mulbc/rgb-badge/hardware/coupon/rev-a/power-library-audit.md

<!-- SPDX-License-Identifier: CERN-OHL-S-2.0 -->

# Coupon Rev A power-library audit

Status: native export at `c84f8ce` completed, but visual/drawing review rejected the charger copper, converter stencil and four symbol headings. Corrections passed first-author native rendering review at `3638b1d`; independent Gate A and the documented assembler shape/stencil review remain pending. See the [correction review](../../../docs/development/power-library-review-3638b1d.md). See the [finding record](../../../docs/development/power-library-review-c84f8ce.md). The selected BQ24074/BQ24392/TS3USB31E replacement libraries now pass source/host audits and await native review; see the [replacement-library audit](power-replacement-library-audit.md) for exact maps, source hashes and recovery corrections.

## Controlled parts

Follow-on correction, 2026-09-16: the DBV0005A F.Fab body and courtyard have changed since the older native review, without copper/paste changes. New permission candidates share that package or the new DBV0006A. See the [permission-library audit](permission-library-audit.md) for the finding, corrected dimensions and pending combined native review. The BQ24074/BQ24392/TS3USB31E replacements subsequently passed [native review at c054cb4](../../../docs/development/power-replacement-review-c054cb4.md); the earlier status above describes their pre-review checkpoint.

| Function | Exact part | Package / project footprint | Controlled source |
|---|---|---|---|
| Standalone charger and NVDC power path | `BQ25616JRTWT` | TI RTW0024A WQFN24, 4 × 4 mm, 0.5 mm pitch, exposed pad / `QFN_TI_RTW0024A_4x4mm_P0.5mm_EP2.7mm` | [TI BQ25616/BQ25616J datasheet](https://www.ti.com/lit/ds/symlink/bq25616.pdf), SLUSDF7A, revised 2022-02 |
| Switched application 3.3 V buck-boost | `TPS631000DRLR` | TI DRL0008A SOT-5X3, 0.5 mm pitch / `SOT5X3_TI_DRL0008A` | [TI TPS631000 datasheet](https://www.ti.com/lit/ds/symlink/tps631000.pdf), SLVSFH3C, revised 2026-08 |
| USB-only 3.3 V LDO | `TLV75533PDBVR` | TI DBV0005A SOT-23-5 / `SOT23_TI_DBV0005A` | [TI TLV755P datasheet](https://www.ti.com/lit/ds/symlink/tlv755p.pdf), SBVS320D, revised 2024-09 |
| USB-current-state inverter | `SN74LVC1G04DBVR` | TI DBV0005A SOT-23-5 / `SOT23_TI_DBV0005A` | [TI SN74LVC1G04 datasheet](https://www.ti.com/lit/ds/symlink/sn74lvc1g04.pdf), SCES214AF, revised 2025-10 |
| Battery-current monitor | `INA232AIDDFR` | TI DDF0008A SOT-23-THIN-8 / `SOT23_THIN_TI_DDF0008A` | [TI INA232 datasheet](https://www.ti.com/lit/ds/symlink/ina232.pdf), SBOSAA2, 2022-12 |
| Four-line USB data/CC ESD | `TPD4E05U06DQAR` | TI DQA0010A USON-10 / `USON_TI_DQA0010A` | [TI TPDxE05U06 datasheet](https://www.ti.com/lit/ds/symlink/tpd4e05u06.pdf), SLVSBO7O, revised 2024-08 |
| USB-C sink/current-state detector | `TUSB320LAIRWBR` | TI RWB0012A X2QFN-12, 1.6 × 1.6 mm, 0.4 mm pitch / `X2QFN_TI_RWB0012A_1.6x1.6mm_P0.4mm` | [TI TUSB320LAI datasheet](https://www.ti.com/lit/ds/symlink/tusb320lai.pdf), SLLSEQ8D, revised 2017-05; [TI RWB package drawing](https://www.ti.com/lit/pdf/MPQF391C) |
| Switched adjustable LED-rail buck-boost | `TPS63020DSJT` | TI DSJ R-PVSON-N14, 4 × 3 mm, 0.5 mm pitch, exposed thermal pad / `VSON_TI_DSJ0014_4x3mm_P0.5mm_EP2.85x1.58mm` | [TI TPS63020 datasheet](https://www.ti.com/lit/ds/symlink/tps63020.pdf), SLVS916I, revised 2019-10 |
| Always-on single-cell fuel gauge | `MAX17048G+T10` | Maxim T822+3 TDFN-EP8, 2 × 2 mm, 0.5 mm pitch / `TDFN_Maxim_T822-3_2x2mm_P0.5mm_EP0.7x1.38mm` | [Analog Devices MAX17048/MAX17049 datasheet](https://www.analog.com/media/en/technical-documentation/data-sheets/MAX17048-MAX17049.pdf), Rev. 7, 2016-12; [21-0168 outline](https://mds.analog.com/api/public/content/tdfn-cu_21-0168.pdf); [90-0065 land pattern](https://mds.analog.com/api/public/content/tdfn-cu_90-0065.pdf) |

The manufacturer PDFs downloaded for this transcription hashed as follows. A changed upstream file requires a fresh comparison rather than a blind hash update.

| Local source name | SHA-256 |
|---|---|
| `bq25616.pdf` | `db1c80794273f68d40f13969888a1da6abc08d4a1ea38b68af8b9a09d7c9834a` |
| `tps631000.pdf` | `b52a4064a8c2cbb4c9dd97f366b398dedcb490ffc9d564245f297536a19b426b` |
| `tlv755p.pdf` | `ee739b0fe51aea50d07b53d0acccad4a0ddeac5bb7aa932bed28dc631ec5305e` |
| `sn74lvc1g04.pdf` | `ac04a53de979125799e57ea5a6dff4138fe53e0eceebe45c31f57523669887d5` |
| `ina232.pdf` | `681ab74ffec4b3b19e30363ca9be52adc75fad089d3ddad59204ebfd52574153` |
| `tpd4e05u06.pdf` | `c167cf1e72a5473a4d2c59b6a3c0251498701da05b7785919b9ceaae3b3e02c6` |
| `tusb320lai.pdf` | `62f7b3f65338e25ebd6fd46ef04474ba806b06b1cc04bc0b3d7b8191b01ca87d` |
| `MPQF391C.pdf` (RWB0012A package drawing) | `694ae75d453a97dffa48fa077e392c728dd668f625f1a7112b03b618e4017633` |
| `tps63020.pdf` | `d117773bb7370fd79377bc70ce987eec3469ea5979547a09df52fca5f95b2e69` |
| `MAX17048-MAX17049.pdf` | `70dc8eef0e012276dcdc58b6dce64af08258304bcf865ceace64e856b8029330` |
| `tdfn-cu_21-0168.pdf` | `01e449022cf1c5e20834fcf2c3587e6a8725e707eed1caa000f095e891be9b0f` |
| `tdfn-cu_90-0065.pdf` | `3448c4e9d300c7b5c2b86d6c67f19fc59c28a91c4b41dfd39fb8cc5a9d4b72eb` |

These are candidate BOM lines, not procurement or fabrication approval. Production lots must use the exact MPN through an authorized distributor or traceable PCBA supply chain. Marketplace listings may be used only for replaceable development samples and must not silently substitute a package or suffix.

## Pin transcription

The `BQ25616JRTWT` symbol preserves all 24 perimeter pins plus the exposed ground pad:

| Pins | Signals |
|---|---|
| 1–4 | `VAC`, `ACDRV`, `D+`, `D-` |
| 5–8 | open-drain `STAT`, `OTG`, open-drain `PG`, `ILIM` |
| 9–12 | active-low `CE`, `ICHG`, `TS`, `VSET` |
| 13–18 | two `BAT`, two `SYS`, two `GND` |
| 19–24 | two `SW`, `BTST`, `REGN`, `PMID`, `VBUS` |
| 25 | exposed `GND_EP` |

The symbol shows `CE` with an inversion bubble and models `STAT`/`PG` as open-collector outputs. `D+` and `D-` remain bidirectional because the charger performs analog source detection. `SW` and `BTST` are intentionally passive switching nodes. Electrical types are ERC aids, not permission to omit the datasheet-required external network.

The `TPS631000DRLR` symbol maps pins 1–8 to `VOUT`, `LX2`, `LX1`, `VIN`, `EN`, `MODE`, `GND` and `FB`. Both `EN` and `MODE` are inputs that must never float in the later circuit.

The DBV symbols do not pretend their shared five-pin package has a shared function: `TLV75533PDBVR` maps `IN`, `GND`, `EN`, `NC`, `OUT`, while `SN74LVC1G04DBVR` maps `NC`, `A`, `GND`, inverted `Y`, `VCC`. `INA232AIDDFR` preserves `IN+`, `IN-`, `GND`, `VS`, `SCL`, `SDA`, `A0`, open-drain `ALERT`. `TPD4E05U06DQAR` preserves the datasheet's `D1+`, `D1-`, `GND`, `D2+`, `D2-`, four `NC` pins and second `GND`; unused ESD pins remain explicit so a later layout cannot mistake them for protected channels.

The `TUSB320LAIRWBR` symbol maps `CC1`, `CC2`, tri-level `PORT`, `VBUS_DET`, tri-level `ADDR`, `INT_N/OUT3`, `SDA/OUT1`, `SCL/OUT2`, `ID`, `GND`, active-low `EN_N` and `VDD` in manufacturer pin order. The dual-use GPIO/I²C signals remain bidirectional in the symbol; `INT_N/OUT3` and `ID` are open-collector outputs, and `EN_N` carries an inversion bubble. These ERC types describe all supported modes and do not select the later circuit configuration.

The `TPS63020DSJT` symbol maps `VINA`, control `GND`, `FB`, two `VOUT`, two `L2`, two `L1`, two `VIN`, `EN`, `PS/SYNC`, open-drain `PG` and the exposed `PGND_EP`. VOUT pin 4 has KiCad's power-output type while pin 5 is passive, so tying the two physical output pads does not produce a false power-output-to-power-output ERC error. Both still map to their manufacturer-numbered VOUT pads. The exposed pad is assigned project pad 15 because KiCad requires a pad number even though TI names it separately from pins 1–14; every copper piece carrying 15 represents the one connected exposed thermal pad.

The `MAX17048G+T10` symbol maps `CTG`, `CELL`, `VDD`, `GND`, open-drain `ALRT`, `QSTRT`, `SCL`, `SDA` and exposed `GND_EP`. `CELL` remains passive because it is not internally connected on the one-cell MAX17048 even though the manufacturer application pin table directs it to the positive battery terminal. The exposed pad is assigned project pad 9 and must connect to ground.

## Land-pattern transcription

The RTW footprint copies TI land-pattern drawing 4211120-3/D:

- 24 signal lands are 0.28 × 0.85 mm on 0.5 mm pitch, with the row centres at ±1.975 mm;
- exposed-pad copper and mask are 2.7 × 2.7 mm and assigned to pin 25. The drawing's 3.1 mm dimension is the opening between opposing signal lands, not the exposed land; the resulting copper clearance is 0.20 mm;
- signal paste is reduced by 0.025 mm per edge to 0.23 × 0.80 mm, and signal mask margin is 0.07 mm. The project uses capsule-ended lands (0.14 mm radius); TI depicts rounded inner ends and square outer ends. This outer-end shape difference remains an explicit assembler/Gate A review item;
- thermal paste is four separate 1.1 × 1.1 mm apertures at `(±0.7, ±0.7)` mm, approximately TI's example 66% area coverage (the project lightly rounds these aperture corners);
- the package's optional nine 0.3 mm thermal vias are not embedded in the footprint. They belong in the PCB layout, where finished drill, annular ring and via fill/capping can be agreed with the assembler;
- courtyard and pin-1 marking are project review geometry, not dimensions copied into the copper pattern.

The DRL footprint copies TI drawing 4224486/G: eight 0.67 × 0.30 mm lands, left/right row centres at ±0.74 mm, and 0.5 mm vertical pitch. The project pin-1 marker sits outside the copper lands beside pad 1.

The shared DBV footprint copies TI drawing 4214839/K: five 1.10 × 0.60 mm lands, left/right row centres at ±1.30 mm, and 0.95 mm vertical pitch. The DDF footprint copies drawing 4222047/E: eight 1.05 × 0.45 mm lands with row centres at ±1.30 mm and 0.65 mm pitch.

The ESD footprint is specifically the base-suffix DQA0010A drawing 4220328/A used by `TPD4E05U06DQAR`, not the later `.B` orderable variant and its DQA0010B via-in-pad geometry. It uses ten 0.565 mm long lands at ±0.4175 mm row centres; signal/NC lands are 0.20 mm wide and ground pads 3/8 are 0.40 mm wide. Substituting a `.B`-suffixed device requires a new footprint and written review.

The RWB footprint copies TI RWB0012A drawing 4221631/B. Pins 1/2 and 7/8 use 0.70 × 0.20 mm side lands centred at `(±0.65, ±0.20)` mm; their paste-only apertures are separately encoded at 0.67 × 0.20 mm. Pins 3–6 and 9–12 use 0.20 × 0.50 mm lands on 0.40 mm pitch, centred at `y = ±0.75` mm with `x = ±0.60, ±0.20` mm. This asymmetry is intentional; the footprint is not a generic 12-pad QFN approximation.

The DSJ footprint copies package drawing 4208212-3/C, thermal-pad drawing 4208549-3/G and land-pattern drawing 4210895-2/E embedded in the current TPS63020 datasheet:

- pins 1–14 use 0.24 × 0.60 mm rounded lands on 0.50 mm pitch at `y = ±1.40` mm, with the example 0.07 mm solder-mask margin;
- exposed-pad copper is a 2.85 × 1.58 mm centre rectangle plus eight same-net 0.775 × 0.20 mm board fingers. The fingers extend the example board copper to 4.40 mm and are centred at `x = ±1.8125` mm, `y = ±0.69, ±0.23` mm;
- the thermal pad has no single full-area paste opening. The 0.125 mm stencil example is encoded as four 1.25 × 0.66 mm centre rectangles at `(±0.725, ±0.46)` mm and eight 0.85 × 0.20 mm side rectangles. These twelve primitives meet edge-to-edge to form four compound apertures, not twelve separated openings. Their total 4.66 mm² area divided by the 5.743 mm² thermal-copper area is approximately 81.14%, consistent with TI's 81% example;
- the drawing's optional 15-via example is not embedded. Via size, finished drill, fill and capping belong to PCB layout and assembler review.

The T822+3 footprint copies Analog Devices/legacy Maxim land pattern 90-0065: eight 0.80 × 0.30 mm signal lands on 0.50 mm pitch, left/right row centres 1.98 mm apart, and a 0.70 × 1.38 mm exposed land. The package-code table in the MAX17048 datasheet maps the exact TDFN orderable part to `T822+3`, outline 21-0168 and this land pattern. Drawing 90-0065 controls copper but does not specify a reduced stencil aperture; the footprint's full-area exposed-pad paste is a documented provisional default that must be reviewed with the assembler before release.

## Intentionally unresolved libraries

No unverified footprint is allowed merely to make the power sheet look complete:

- `USB4505-03-0-A`: the owner supplied GCT drawing A2; both pages and the enlarged recommended layout were visually inspected. The separate [connector audit](usb-connector-audit.md) controls the recovered symbol and draft footprint. Host mapping/geometry/fault checks and [native rendering at `bf1627c`](../../../docs/development/usb-connector-review-bf1627c.md) pass; the 0.80 mm stack-up/process qualification and undimensioned cutout reliefs remain open. The footprint contains no `Edge.Cuts`.
- The latching slide switch, remaining converter/charger passives, battery connector and NTC network remain for the next library/capture increments. The switch and battery connector cannot be frozen before exact mechanical parts are selected.

## Automated and native review

`python3 tools/check-power-libraries.py` checks twelve exact MPN properties, 132 logical pins and eleven transcribed land maps including the three replacement libraries, the BQ and DSJ exposed copper/paste splits, the DQA ground-land distinction, the RWB side-pad paste reduction and pin-1 markers. Dimension tables can repeat a transcription error: this happened at `c84f8ce`. A separate geometry guard now rejects touching/overlapping bounding boxes of distinct copper-pad numbers, independently of those tables. It is deliberately restricted to the current unrotated rectangular/rounded-rectangle power footprints and allows connected same-number thermal pieces; it is not PCB DRC. Additional checks constrain top-facing symbol headers, BQ paste/mask settings and DSJ nominal paste coverage. `tools/check-kicad.sh` also requires KiCad 10 to load and export every controlled symbol and all three footprint views.

For the native render review, verify:

- BQ pins 1–6 run down the left package edge, 7–12 across the bottom, 13–18 up the right and 19–24 across the top when viewed from above;
- BQ pin 25 is one continuous central copper/mask land, while the paste-only view shows exactly four separated square apertures;
- the BQ symbol shows the `CE` inversion bubble plus open-drain `STAT` and `PG` outputs;
- TPS631000 pad 1 is upper-left, pins 1–4 run down the left, and pins 5–8 run up the right;
- DBV/DDF pads count counter-clockwise from upper-left; both DBV parts reuse identical copper without sharing their pin names;
- DQA pads 1–5 run down the left and 6–10 run up the right, with wider ground lands only at pins 3 and 8;
- RWB pins count counter-clockwise from side pad 1; side lands are visibly longer than their paste apertures, while top/bottom lands include paste directly;
- DSJ pins 1–7 run left-to-right across the top and 8–14 right-to-left across the bottom; copper shows a centre pad with four fingers per side, while paste shows four compound thermal apertures made from twelve rectangular primitives;
- T822+3 pads 1–4 run down the left and 5–8 run up the right around the narrow exposed pad; full-area exposed-pad paste is visible and remains a documented DFM item;
- distinct copper pads remain separated, silkscreen avoids lands, and symbol headings clear their pins. Fabrication outlines and fabrication-only text may overlay copper in combined review views; they are not printed silkscreen and must not be mistaken for copper shorts.

A clean automated run is necessary but is not DRC, thermal analysis, USB compliance, assembler DFM, battery safety review or independent Gate A approval.
