mulbc/rgb-badge/hardware/coupon/rev-a/3v3-converter-capture-contract.md

<!-- SPDX-License-Identifier: CERN-OHL-S-2.0 -->

# Coupon Rev A 3.3 V application converter capture contract

Status: **provisional root-linked circuit, 2026-10-05**. The TPS631000 converter and one physical-switch control pole are now in the canonical KiCad schematic, with the former `+3V3_APP` source flag removed. The converter VIN source is still a flagged draft boundary, its EN switch/footprint remains subject to mechanical review, and no board has been built. This increment does not select the battery, charger ISET, or a PCB order. It applies the hard-OFF decision in [ADR 0004](../../../docs/decisions/0004-standalone-charging-and-hard-off-state.md), the independently switched gauge in [ADR 0015](../../../docs/decisions/0015-switch-fuel-gauge-with-application.md), the provisional parallel-capacitor target in [ADR 0017](../../../docs/decisions/0017-parallel-3v3-converter-capacitors.md), and PWR-003/004/008 in [requirements](../../../docs/requirements.md).

## Circuit boundary and defaults

| TPS631000DRLR pin | Planned net or connection | Capture condition |
|---|---|---|
| 1 VOUT | `+3V3_APP` | Output capacitor and divider upper resistor return here; do not connect to USB-only 3.3 V. |
| 2 LX2, 3 LX1 | Opposite ends of the 1 µH inductor | Short, wide switching loop per TI layout guidance; no global power labels on LX. |
| 4 VIN | Protected BQ24074 charger `OUT` / `SYS` after its voltage/permission design is completed | Input capacitor to local ground. Never connect to the gauge's `+BAT_GAUGE_SW` pole. The BQ24074 specifies 4.3–4.5 V regulated OUT with a sufficient USB input; battery-only OUT is supplied through the BAT FET. Bound switching/fault transients separately within the converter's 1.6–5.5 V operating range. |
| 5 EN | The application pole of the latching ON/OFF switch drives it high from a valid protected source; an independent resistor pulls it to GND in OFF and throughout an open/bouncing contact. | Switch contact may drive *only control current*, not application load. Candidate 100 kΩ pull-down needs an exact resistor MPN, contact and OFF-leakage audit; it is not yet captured. Do not rely on MCU GPIO or an internal pull-down. |
| 6 MODE | GND | Fixed auto-PFM default for light-load efficiency; do not float or make boot behavior firmware-dependent. |
| 7 GND | Local power return | Tie input/output capacitors and feedback lower resistor into a suitable ground layout. |
| 8 FB | Junction of 511 kΩ VOUT-to-FB and 91 kΩ FB-to-GND | Keep the sense node clear of LX and high-current traces. |

The gauge uses a **separate** switch pole for its cell feed. VLED needs the physical ON condition **and** a hardware-qualified display request, with VLED disabled at boot/reset/programming. Sharing an ON-permission signal with the LED interlock is a later reviewed circuit decision, not a reason to route LED current through the switch. When OFF, the 3.3 V converter must disconnect its output and the unpowered application must not be back-fed from USB data, gauge I²C, debug pads, or another rail. TI calls the TPS631000 behavior *true shutdown with load disconnect*, but whole-board OFF isolation and <50 µA remain measured requirements. The separately powered USB-only logic is allowed to operate when USB is attached while the application switch is OFF.

**Planned steady source states for `SYS` / converter VIN:** These are BQ24074 device behaviors from [TI's datasheet](https://www.ti.com/lit/ds/symlink/bq24074.pdf), §§8.5 and 9.3.2–9.3.4, applied to the accepted Type-C-only permission policy. They do not bound attach/detach overshoot or establish pack capability.

| State | BQ24074 OUT source | Converter-input check |
|---|---|---|
| USB absent, battery connected | Battery through BAT-to-OUT FET | Check low protected-pack end voltage, BAT-to-OUT drop and converter load capability; charging-voltage maximum is specified as 4.23 V at BAT under the datasheet condition. |
| USB-A or Type-C default-current, charger standby `(EN1, EN2) = (HI, HI)` | Battery through BAT-to-OUT FET; input FET OFF | Even with USB VBUS present, do not treat OUT as a 5 V rail or allow charger-supplied application current. Depleted/absent-pack recovery remains unguaranteed. |
| Qualified Type-C 1.5 A/3 A, charger in fixed-ILIM normal mode | Input-fed regulated OUT, **4.3–4.5 V** with sufficient headroom; DPPM may lower it, then battery supplements | Use 4.5 V for the steady high CIN DC-bias screen; check 2.7 V minimum required for TI's full-load example at discharge/DPPM corners. |
| USB input fault, source revocation or switching | Input FET turns off under standby/OVP and OUT reverts to battery when present | Capture and measure any OUT overshoot/ringing and temporary undershoot separately; 4.5 V regulated maximum is not a transient maximum. |

## Manufacturer starting point and arithmetic

TI's [TPS631000 Rev. C datasheet](https://www.ti.com/lit/ds/symlink/tps631000.pdf), §§4, 5.3, 5.5, 6.3 and 7.2, gives the 2.7–4.3 V, 3.3 V/1.5 A typical design and these proposed parts/values. The precise passive order codes below are **candidates from TI's example**, not yet audited land patterns or a released BOM.

| Function | Starting value / candidate | Unresolved qualification |
|---|---|---|
| U | `TPS631000DRLR`, already audited project-local DRL0008A library | Native circuit ERC/XML, thermal and startup validation. |
| L between LX1/LX2 | 1 µH `DFE252012P-1R0M=P2` (Murata), ±20% initial tolerance, 42 mΩ max DCR, 2.5 × 2.0 × 1.2 mm max | Murata distinguishes 4.3 A at a 30% inductance drop from **3.2 A at a 40 °C winding temperature rise**, both referenced to 20 °C ambient. The [source and land audit](3v3-inductor-footprint-audit.md) stages an unplaced exact-MPN symbol and footprint. In-enclosure thermal/current derating, native rendering and placement height remain open. |
| CIN1, CIN2 | Two parallel 22 µF `GRM187R61A226ME15` (Murata), provisional coupon target per ADR 0017 | Murata's [product/characteristic listing](https://ds.murata.com/simsurfing/mlcc.html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) lists **10 V**, X5R, ±20%, 0603, 0.8 mm height, and in-production status. TI's Table 7-4 incorrectly labels the exact-part row 6.3 V; use the manufacturer value after checking the current orderable suffix. One Murata curve shows 6.462 µF at BQ24074's 4.5 V regulated OUT maximum under the stated 25 °C condition. Exact land/placement, combined derating, charger OUT startup and transients remain unqualified. |
| COUT1, COUT2 | Two parallel 47 µF `GRM219R60J476ME44` (Murata), provisional coupon target per ADR 0017 | Murata's [part/model list](https://www.murata.com/-/media/webrenewal/tool/library/common-pdf/dynamic-model/component-list-d-mlcc-2506.ashx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) lists **6.3 V**, X5R, ±20%, 0805 and 0.95 mm maximum height. One Murata curve shows 16.876 µF at 3.3 V / 25 °C; exact land/placement, combined derating and startup/transients remain unqualified. |
| Feedback | Upper: Panasonic `ERJ2RKF5113X` (511 kΩ); lower: `ERJ2RKF9102X` (91 kΩ), proposed exact parts | Panasonic's [511 kΩ](https://industrial.panasonic.com/ww/products/pt/general-purpose-chip-resistors/models/ERJ2RKF5113X) and [91 kΩ](https://industrial.panasonic.com/ww/products/pt/general-purpose-chip-resistors/models/ERJ2RKF9102X) pages specify 0402, 0.1 W, ±1% and ±100 ppm/K each. Two project-local symbols are **staged but unplaced**, using the manufacturer's unhyphenated order codes; they reuse the earlier ERJ2 passive geometry. Native KiCad 10.0.6 rendering passed first-author visual review at [8014947](../../../docs/development/3v3-passive-library-review-8014947.md) before this text-only spelling correction; recheck their displayed values at the next converter export. Panasonic's [recommended land pattern](https://industrial.panasonic.com/cdbs/www-data/pdf/RDM0000/DMM0000COL17.pdf) (24 Dec 2025) gives a 0.5–0.6 mm inner gap, 1.4–1.6 mm outer span, and 0.4–0.6 mm land width for general-purpose ERJ 1005/0402; reused `R_Panasonic_ERJ2_0402` has 0.5, 1.5, and 0.5 mm respectively. This is a drawing comparison, not assembler approval. TI requires the lower resistor ≤100 kΩ. |
| EN pull-down | Panasonic `ERJ2RKF1003X` (100 kΩ), proposed reuse | Exact-MPN symbol and footprint already occur in the row/controller design. Check contact leakage, OFF-current budget and possible effect of VLED permission circuitry when the physical switch is specified. |

With TI's 500 mV nominal feedback reference, the nominal output is `0.500 × (1 + 511/91) = 3.3077 V`. An **illustrative, independent ±1% initial tolerance** on both resistors combined with TI's 495–505 mV reference limits gives `3.2196–3.3981 V`. For an illustrative PCB resistor excursion of **60 °C from its reference temperature**, allowing the two ±100 ppm/K TCRs to oppose each other adds ±0.6% drift *per resistor*; together with initial tolerance and the same feedback limits, the calculated range is `3.1871–3.4330 V`. This is a sensitivity screen, not a guaranteed delivered voltage or an assertion of the final PCB temperature: long-term drift, loading, routing drop, ripple and transients require a full worst-case check. Divider standing current is about `3.3077 V / (511 kΩ + 91 kΩ) = 5.49 µA` while ON; this divider belongs entirely on the switched output, so it cannot drain the battery through an enabled output in hard OFF.

**Consumer voltage screen:** The [ESP32-S3-WROOM-1U module](https://documentation.espressif.com/esp32-s3-wroom-1_wroom-1u_datasheet_en.pdf) requires 3.0–3.6 V at its supply pads; the [TLC59581](https://www.ti.com/lit/ds/symlink/tlc59581.pdf) specifies 3.0–5.5 V VCC; the [TS3USB31E application USB switch](https://www.ti.com/lit/ds/symlink/ts3usb31e.pdf) specifies 2.25–4.3 V VCC; the [INA232](https://www.ti.com/lit/ds/symlink/ina232.pdf) specifies 1.7–5.5 V; and [74HC4514](https://www.nexperia.com/product/74HC4514PW) specifies 2.0–6.0 V. These are the principal active loads identified so far, not a complete pad-by-pad audit. The illustrative static extremes leave only **187 mV below** the module's 3.0 V minimum and **167 mV above** the static 3.433 V maximum before reaching its 3.6 V upper limit. TI's 150 mV response to a 1 A load step is a *typical* advertised result, not a guaranteed maximum or a license to spend almost all 167 mV. Actual droop/overshoot at the module, RF/BLE bursts, display transitions, startup and charger/source steps must remain within every load's limits over component and temperature corners. If that cannot be shown, revisit the feedback tolerance/value or capacitance rather than accepting a marginal rail.

The candidate 100 kΩ EN pull-down, if connected as specified and if **only** the published ±0.3 µA maximum EN input bias at 5.5 V opposes it, develops at most 30 mV in OFF; TI lists a 0.5 V minimum falling threshold. This is a component-level margin illustration, **not** a bound on switch contamination, PCB leakage, an attached debug tool, or an upstream driver. In ON it draws about 27–43 µA from a 2.7–4.3 V control source; the closed switch contact must keep EN above TI's 1.2 V rising threshold at all valid SYS voltages. The pull-down must return to GND, never to unswitched SYS.

**Exact-part DC-bias evidence (owner-supplied Murata SimSurfing CSV):** `GRM219R60J476ME44_InProduction.csv`, SHA-256 `79839e9d42e739c23f68490a2ea4248ca1c6cb45026c2a8897408973abaaa57e`, contains both `GRM219R60J476ME44` and `GRM187R61A226ME15` columns. Its header states capacitance at **25 °C, AC 0.5 Vrms**. Values below are linearly interpolated between adjacent CSV samples and rounded to three decimal places; they are characteristic-curve values, not minimum specifications or board measurements.

| Candidate and DC bias | Curve capacitance | Illustrative 80% of curve | TI minimum |
|---|---:|---:|---:|
| CIN at 4.3 V | 6.811 µF | 5.449 µF | 4.2 µF |
| CIN at 4.5 V (BQ24074 regulated OUT maximum) | 6.462 µF | 5.169 µF | 4.2 µF |
| CIN at 5.0 V | 5.723 µF | 4.579 µF | 4.2 µF |
| CIN at 5.5 V | 5.131 µF | 4.105 µF | 4.2 µF |
| COUT at 3.3 V | 16.876 µF | 13.501 µF | 10.4 µF |
| COUT at 3.433 V (illustrative high static rail) | 16.133 µF | 12.906 µF | 10.4 µF |

The 80% column applies the catalog ±20% initial capacitance tolerance *as a sensitivity illustration* to the **single-part** characteristic curve; it is not a validated combined worst-case model. The [BQ24074 datasheet](https://www.ti.com/lit/ds/symlink/bq24074.pdf), §8.5, specifies **4.3–4.5 V** regulated OUT for this exact variant when the input has sufficient headroom; §9.3.4 describes lower OUT voltage under DPPM/supplement and battery-only supply. Thus 5.5 V normal USB VBUS does **not** imply 5.5 V steady converter VIN. At 4.5 V the single CIN illustration leaves 0.969 µF before temperature and aging. As a further *illustrative*, independent 15% reduction for X5R temperature variation gives 4.394 µF per CIN at 4.5 V and 10.970 µF per COUT at the illustrative 3.433 V rail high: only 0.194 and 0.570 µF respectively before aging and other effects. These multiplications are sensitivity screens, not guaranteed lower bounds. [ADR 0017](../../../docs/decisions/0017-parallel-3v3-converter-capacitors.md) provisionally doubles each position for the coupon, subject to close placement and combined manufacturer derating; two parts do not make the curve a guaranteed minimum. At the converter's 5.5 V operating input boundary a **single** CIN illustration misses the minimum by 0.095 µF even *before* the extra temperature term, but that input voltage is a fault/transient scenario, not the BQ24074's regulated steady OUT. Verify final SYS transient maximum, exact lot curves, temperature, aging and assembled rail behavior before release.

TI specifies >1.65 V for startup, but its 1.5 A example and front-page output-current claim require VIN ≥2.7 V at 3.3 V output. Do not infer full-load operation down to converter UVLO or the cell protector's cutoff. Confirm minimum `SYS` at the final protected-pack end of discharge and while source qualified charging is present, with simultaneous ESP32/radio/logic loads. TI's typical example output current is a **capability condition**, not a measured badge load or efficiency promise.

**Inductor first-order screen:** Applying TI's boost-mode Equation 3 to the *example* 1.5 A output at VIN 2.7 V, VOUT 3.3 V, assumed 90% efficiency, 0.8 µH (the candidate's nominal 1 µH minus its initial 20% tolerance), and 1.8 MHz (TI's stated minimum switching frequency) gives `D = 0.1818`, average inductor current `2.037 A`, half ripple `0.170 A` and `Ipeak ≈ 2.207 A`. TI's suggested 20% saturation margin would require `≥2.649 A` against Murata's **4.3 A 30%-drop** figure at the specified reference condition. The separate **3.2 A / +40 °C** criterion is not a board thermal result; its winding rise, local ambient, inductance under DC bias, and actual peak current must be qualified in the small enclosure. Efficiency was assumed, not measured. A pack/charger SYS below 2.7 V or a higher load needs a fresh calculation.

At the same 2.7 V / 3.3 V / 1.5 A example, replacing only the assumed efficiency in Equation 3 gives this **sensitivity screen**, not a guaranteed efficiency curve. TI's 2.6 A **minimum DC-tested** switch peak-current limit is a separate IC constraint; operating current can depend on propagation delay and external parts. The Murata 4.3 A inductance-drop and 3.2 A temperature-rise conditions are also distinct.

| Assumed efficiency | Calculated inductor peak | Margin to TI 2.6 A DC-tested minimum | TI 20% inductor saturation target |
|---:|---:|---:|---:|
| 90% | 2.207 A | 0.393 A | 2.649 A |
| 85% | 2.327 A | 0.273 A | 2.793 A |
| 80% | 2.462 A | 0.138 A | 2.955 A |
| 75% | 2.615 A | −0.015 A | 3.138 A |

This table does not establish that the badge draws 1.5 A or that efficiency falls to 75%. It shows why a full-load claim needs measured or bounded efficiency at the **actual** minimum SYS, output load and temperature, with the inductor's DC-bias inductance and winding rise considered together. The 20% saturation target is not extra margin to the IC's current limit.

## Next capture and release checks

1. The two candidate capacitor libraries have a [first-author reference-sheet audit](3v3-capacitor-footprint-audit.md): GRM18 0603 is reused, GRM21 0805 and two exact-MPN symbols are staged but unplaced. Their native export/visual review passed at [8014947](../../../docs/development/3v3-passive-library-review-8014947.md). Reconcile current approval drawings/orderable suffixes, then verify effective-capacitance curves under temperature/aging and placement. The [inductor land audit](3v3-inductor-footprint-audit.md) stages its unplaced library; check native rendering and assembler DFM. Recheck the corrected feedback symbol values during the next native export. Check the inductor-current margin against TI's worst operating-condition equation and derating, not only its table saturation value. Compare the output tolerance screen with every 3.3 V consumer's guaranteed range.
2. Finish the protected `SYS` source and exact two-pole switch (including orientation/contact sequencing), then wire VIN and EN. The USB-only rail must remain distinct. Do not make a draft PWR_FLAG look like a real `SYS` source.
3. Capture a dedicated schematic sheet, extend exported-netlist invariants to the eight IC pins, feedback network, switched enable, MODE, caps, inductor and output loads; require zero configured ERC. Inspect native KiCad 10.0.6 PDF and footprint layers. Replace/reconcile old draft supply flags at the real source boundary.
4. Before Gate A, calculate tolerance/ripple/derating and startup/inrush over minimum pack voltage, charging and 5.5 V input envelope; review hot loops, thermal copper, EMI and assembled thickness. On the coupon, log the rail **at the ESP32-S3 pads** during switch bounce, USB attach/detach, RF bursts, simultaneous LED switching and output load steps, including 3.0 V minimum and 3.6 V maximum acceptance checks with instrument bandwidth/probe method recorded. Measure OFF rail voltage and battery current both before firmware has ever run and after normal use, with USB absent and present separately.

Sources: [TI TPS631000 Rev. C (August 2026)](https://www.ti.com/lit/ds/symlink/tps631000.pdf) for electrical limits, Equation 3 and its reference circuit; [Murata DFE252012P series sheet](https://www.murata.com/~/media/webrenewal/products/inductor/chip/tokoproducts/wirewoundmetalalloychiptype/m_dfe252012p.ashx) for distinct current limits, inductance tolerance, dimensions and land-pattern sketch; Murata part/model listings linked in the table for nominal MLCC ratings; owner-supplied SimSurfing exact-part CSV identified by SHA-256 above for **25 °C DC-bias characteristics only**; [power library audit](power-library-audit.md) for the already audited IC symbol/footprint. Full temperature/aging/lot derating and assembly evidence remain to be gathered.
