mulbc/rgb-badge/CONTEXT.md

<!-- SPDX-License-Identifier: CERN-OHL-S-2.0 -->

# Project context

## Purpose

Create a small, manufacturable 48 × 16 RGB wearable badge that preserves the 1.95 mm pixel pitch of the referenced FOSSASIA Badge Magic board. The owner intends to develop the electronics, firmware and enclosure with AI assistance, then have a turnkey PCBA supplier assemble the SMT hardware.

## Complete power proposal, 2026-10-05

[ADR 0018](docs/decisions/0018-complete-power-architecture-proposal.md) and the [whole-system proposal](docs/design/power-architecture-2026-10-05.md) recommend a protected USB detector domain plus a separate reverse-blocking charger gate, the existing charger/converters, a buffered switched gauge and a lower conditional charge-current target. Status is **proposed for engineering review, not accepted as a complete power circuit**. ADR 0024 has since selected the exact protected LP452845 assembly as the Rev A design target; supplier stock and physical qualification remain open. Six consolidated holds cover pack, USB faults/inrush, permission startup, gauge transitions, hardware display interlock and thermal/fit. The limited switch/3V3 and temperature captures implement accepted directions but do not complete the charger or change an accepted current setting. Review by complete architecture → complete schematic → PCB/mechanical batches; local KiCad CLI 10.0.6 is now accessible without owner command/upload cycles. Existing reviews at `0764245` remain the baseline for preceding sheets.

**USB current coordination, 2026-10-07:** [proposed ADR 0022](docs/decisions/0022-lower-fixed-usb-input-limit-proposal.md) screens a single already-audited 3.65 kΩ BQ24074 ILIM resistor. Its calculated 0.361–0.476 A input interval avoids the earlier steady-state overlap with the published 0.850 A minimum eFuse breaker test point, before auxiliary current and resistor tolerance. This is a simpler proposed direction, not a selected schematic setting; exact-pack charge timing, input transients and default-off hardware permission remain open.

**Charger permission boundary, 2026-10-07:** The [pin-level review](docs/design/charger-permission-boundary-2026-10-07.md) maps the proposed E1 enable, AUP inhibit, supervisor RESET and BQ fixed-mode pins without connecting them to the canonical schematic. BQ `EN2` cannot yet be assigned to a qualified source with both valid-input timing and fault-voltage bounds. The current USB permission outputs remain test points, not charger controls.

**EN2 candidate, 2026-10-07:** [Proposed ADR 0023](docs/decisions/0023-charger-en2-local-clamp-proposal.md) and its [DC screen](docs/design/charger-en2-shunt-screen-2026-10-07.md) choose a local 2.5 V shunt supplied through 10 kΩ from admitted charger input as the next capture candidate. Calculated shunt-current and power margins exist within the stated input range, conditional on an assumed EN2 input-current allowance. Exact EN2 leakage at the clamped voltage, dynamic source transitions and compact-board resistor temperature remain unqualified; H3 is not closed.

**Battery-temperature sourcing update, 2026-10-05:** [ADR 0019](docs/decisions/0019-board-mounted-battery-temperature-sensing.md) accepts trialing a battery-facing PCB NTC wired directly to charger TS with a protected two-wire pack. Cell-to-board temperature error and faults must be tested before freeze; no NTC safeguard is removed. The [pack screen](docs/sourcing/pack-screen-2026-10-05.md) first identified bare-wire LiPol `LP503055` as the leading technical comparator; ADR 0024 now chooses the connectorized `LP452845` assembly for Rev A design. No pack has been ordered or qualified.

**Rev A pack/temperature direction, 2026-10-09:** [ADR 0024](docs/decisions/0024-lp452845-pack-and-temperature-window.md) selects the exact LP452845/PHR-2 drawing as the working design target. TI's BQ24074 native 10 kΩ TS window is wider than this pack's +10…+45 °C charge rating. The design now adds a battery-facing `TMP390A2DRLR` hardware hot/cold gate at nominal 40/15 °C while retaining an exact 10 kΩ Murata NTC at charger TS and its safety timer. The corrected [mechanical screen](mechanical/lp452845-swap-screen-2026-10-09.md) uses JST's actual 9.2 × 10.2 mm footprint courtyard, shifts the pack 1.5 mm right, moves one output capacitor and repacks 43 0402 boxes; this is an unrouted XY trial. Pack availability, exact polarity, continuous-discharge suitability and physical sensor-to-cell error remain unverified.

**Connected temperature subcircuit, 2026-10-10:** The [root-linked sheet](hardware/coupon/rev-a/charger-temperature.kicad_sch) connects the selected Murata NTC, TI TMP390 and AUP buffer, five supporting passives and two test pads to named `CHARGER_TS` and `CHARGER_GATE_EN` boundaries. [First-author KiCad review](docs/development/charger-temperature-capture-review-2026-10-10.md) passed zero-violation ERC, exact native XML matching 420 PCB items/1,562 logical pins, and page-15 visual inspection. BQ TS, E1 EN, the pack/header and remaining charger circuit are not connected; no temperature-protection function has been measured.

**Charger-parts follow-on, 2026-10-10:** [ADR 0024](docs/decisions/0024-lp452845-pack-and-temperature-window.md) selects exact Panasonic `ERA2AEB2491X` as the 2.49 kΩ charger ISET resistor, retaining the ±1% total resistance/current envelope; its project-local symbol uses the audited ERA2 land. The [JST `S2B-PH-SM4-TB` footprint](hardware/coupon/rev-a/jst-ph-header-library-audit.md) is staged with numbered contacts and retention lands. Exact delivered-pack polarity and mating orientation must be checked before it is connected.

**Provisional charger core, 2026-10-10:** [The root-linked BQ24074 sheet](hardware/coupon/rev-a/charger-core.kicad_sch) now joins TS to the battery-facing NTC and OUT to the application SYS net, and places exact 2.49 kΩ ISET, one 3.65 kΩ ILIM, and IN/BAT/OUT bypass parts. [ADR 0022](docs/decisions/0022-lower-fixed-usb-input-limit-proposal.md) selects the lower ILIM part for provisional capture. EN2 and EN1 are currently grounded for 100 mA fallback; ILIM is inactive until a qualified EN2 source exists. ITERM and TMR intentionally use TI's built-in termination and active safety timers. Input and protected-pack nets have explicitly draft source flags solely for ERC because neither physical gate nor pack connector is captured. KiCad 10.0.6 yielded zero configured ERC violations and complete native XML with 426 PCB items/1,589 logical pins; the 16-page export was visually reviewed. This is not a functional charger and does not resolve input gating, pack polarity, capacitor bias/voltage, thermal or Gate A.

**Final-board space finding and correction, 2026-10-05:** The [preliminary component-space screen](mechanical/component-space-screen-2026-10-05.md) moves the three LED-driver courtyards right to clear the `LP503055` body, then projects all other 151 currently captured coupon footprint instances onto the 106 × 32.5 mm trial final board. Its initial assumption that the entire battery outline must be component-free leaves 98.69 mm² nominally and 96 items unplaced in simple first-fit packing. The owner correctly noted that the pack is a separate wired assembly supported above the PCB. A conditional XY screen moving 77 0402 resistors/capacitors beneath that outline raises nominal outside-space remainder to 252.69 mm², with 22 of 74 outside items unplaced in the same crude packing pass. Height, insulation, thermal coupling and circuit locality remain unverified; neither screen proves fit or no-fit, and no requirement relaxation is justified yet.

**Grouped mechanical fit trial, 2026-10-06:** The [to-scale rear/section study](mechanical/fit-trial-2026-10-06.md) places all 32 row-switch courtyards by function and gives 77 0402 parts conditional XY positions beneath the separate LP503055 pack. Eight other captured coupon parts plus the unfinished power, connector, RF and mounting items remain unplaced; the optimistic 0402 section totals 10.75 mm of an 11 mm case with only 0.25 mm nominal margin before assembly tolerances. This is a useful layout finding, not a KiCad PCB, fit approval or reason by itself to relax the product requirements.

**Battery-connector screen, 2026-10-06:** The [JST GH/PH and Molex comparison](mechanical/battery-connector-screen-2026-10-06.md) treats each as a candidate, not a selected pack termination. An illustrative JST PH 8 × 9.6 mm pocket has no free position in the original grouped plan even before small-part first-fit. Pack availability, polarity, actual wire/crimp fit and final connector geometry remain unconfirmed.

**Connector-first follow-on, 2026-10-06:** A [Molex PicoBlade 8 × 8 mm pocket trial](mechanical/connector-first-trial-2026-10-06.md) moves the top-edge switch and decoder, then repacks the row FETs. The pocket is collision-free in XY, but only 28 of 32 row FETs fit and eleven captured parts remain unplaced overall; charger/VLED/protection/support hardware remains absent. The connector family has manufacturer AWG 28 reference-current data, but the pocket is not an audited footprint and the pack is not selected. This result directs effort back to the coupon power circuit and/or a material row-stage or battery change rather than more arbitrary first-fit movement.

**Dual row-package area screen, 2026-10-06:** [ADR 0020](docs/decisions/0020-dual-row-mosfet-package-proposal.md) proposes evaluating 16 complementary `DMC1229UFDB-7` N/P packages in place of the 32 separately packaged row FETs, without changing the captured circuit yet. The [conditional XY trial](mechanical/dual-row-package-screen-2026-10-06.md) places all retained non-row captured parts, candidate pair courtyards and four proposed power-IC package minima around the connector pocket. About 254 mm² of nominal courtyard area is recovered. Full power support, routing, copper, thermal and vertical fit are still unproven, and a real current/pin/land review must precede any coupon substitution.

**VLED placement follow-on, 2026-10-06:** The [tightened conditional screen](mechanical/dual-row-package-screen-2026-10-06.md) moves the decoder to the upper-right edge and groups the staged, default-disabled TPS63020 with all twelve passives in an 11 × 9.3 mm lower-right bay. Its first input and output capacitor centres are each 2.974 mm from the IC centre, still without routes or a switching-loop check. All sixteen proposed row-package courtyards fit the first-fit variant with the INA232 monitor IC box omitted; adding it leaves one pair box unplaced in that heuristic. [ADR 0021](docs/decisions/0021-external-battery-current-measurement.md) now accepts external current measurement and omits the on-board monitor/shunt from capture. This is not proof of complete fit: charger/input support and full routing remain absent.

**VLED routing follow-on, 2026-10-06:** A [separate local KiCad trial](docs/development/vled-routing-trial-2026-10-06.md) connects both inductor terminals and the first input/output capacitor positives with twelve 0.20 mm geometry-probe segments. Native DRC reports zero geometry violations and twenty open connections. No current/thermal suitability is established. The divider was reordered within its existing three boxes to bring its grounded end nearer the IC control-ground pad; all ground/feedback/interlock and other-board routing remain open.

**Candidate row-package library, 2026-10-06:** A [first-author Type B footprint](hardware/coupon/rev-a/dual-row-package-library-audit.md) now transcribes the manufacturer's `DMC1229UFDB-7` eight-land suggested pattern into a 3 × 3 mm project courtyard; the XY screen reads that actual candidate courtyard. Native KiCad 10.0.6 renders it and the unchanged 410-item coupon passes zero-violation ERC/1,537-pin netlist. The footprint is unpopulated; independent numeric pin-map, stencil/assembly, compact-board thermal and row-circuit review remain required before any schematic or BOM substitution.

**Provisional application-power capture, 2026-10-05:** [JS202011JCQN](hardware/coupon/rev-a/slide-switch-library-audit.md) now supplies one root-linked latching-switch control contact to the TPS631000 EN input, with a 100 kΩ OFF pull-down; the TPS631000 converter sheet is root-linked and the former `+3V3_APP` PWR_FLAG removed. Its input `+SYS_APP_IN_DRAFT` still has an explicit PWR_FLAG because charger OUT is absent. The switch's second pole and the staged gauge supply flag remain open pending I²C isolation. KiCad 10.0.6 zero-violation ERC and complete XML pass at 410 PCB items / 1,537 logical pins; pages 13–14 were visually reviewed. The vertical JCQN is not frozen for the top-edge mechanical requirement; throw direction, manufacturer land drawing, fit and OFF current remain open. This does not complete the power schematic or close the ADR 0018 holds.

## Active simplification — ADR 0013

The owner accepted **Type-C-only charging** on 2026-09-18. This section supersedes the historical BC1.2/SDP/boost descriptions below. [ADR 0013](docs/decisions/0013-type-c-only-fixed-current-charging.md) keeps OFF charging and charge-through operation only for Type-C sources advertising 1.5 A/3 A. USB-A/default-current sources provide data while ON from battery power, but no charging or charger PowerPath input. Depleted-battery USB recovery on those sources is not guaranteed.

The revised source removes BQ24392 and its support parts, eleven permission gates, three dual buffers and obsolete grant pull resistors/test pads: **47 fewer PCB items**. Current totals: **396 items / 1,492 logical pins, eleven pages**. The libraries remain 46 symbols / 27 footprints, including retained historical candidates. Native KiCad 10.0.6 at `12a134f` passed zero-violation ERC, complete exported-netlist checks and first-author visual review of the three revised USB sheets. TP21 correctly observes conditioned OUT2, closing the cb81e86 finding. See [review](docs/development/type-c-only-review-12a134f.md).

The fixed ILIM uses the audited 3.65k/3.48k precision pair permanently in parallel, with no analog switch. ADG4612 and its leakage/supply screening are historical, not active blockers. Remaining power work: protected input, VBUS qualification and physical standby control; charger/pack/NTC/timer/thermal design; converter and gauge capture; whole-port budget and layout. Flag meaningful simplification opportunities to the owner before expanding complexity.

## Active input-voltage correction — ADR 0014

[ADR 0014](docs/decisions/0014-usb-voltage-envelope-and-logic-ldo.md) corrects the normal USB upper boundary to 5.5 V. U29 now uses TPS70933DBVR with EN intentionally open; source totals remain 396 items / 1,492 logical pins, libraries 47 symbols / 27 footprints. Native U29 review passed at bad43fa; see the input-library checkpoint below. The prior 12a134f review applies to the preceding U29 circuit. [Protection screening](hardware/coupon/rev-a/usb-input-protection-screening.md) has a calculated OVLO window, but no selected/captured protection IC or transient closure. No user rerun is requested for this intermediate checkpoint. All 147 host tests passed. The owner supplied the exact-family Murata characteristic PDF; [C32 screening](hardware/coupon/rev-a/c32-characteristic-review.md) supports retaining the capacitor in the draft. The source-access blocker is closed; combined bias/temperature/aging limits and bench stability remain qualification items, not another immediate document request.

## Input-protection library checkpoint (2026-09-20)

Two unplaced TPS25947 candidates now share an audited RPW0010A library: [audit and electrical findings](hardware/coupon/rev-a/input-protection-library-audit.md). Libraries contain **49 symbols / 28 footprints**, while the schematic remains 396 items / 1,492 pins. The 472 clamp/active-limit variant could remove the OV divider now that U29 has wider input tolerance, but neither variant is selected. PG startup levels and the low end of the current threshold prevent treating nominal settings as qualification. Owner KiCad 10.0.6 at bad43fa passed configured zero-violation ERC, full native XML and first-author U29/candidate geometry review; see [evidence](docs/development/input-review-bad43fa.md). A derived RPW numbered review now removes duplicate corner numerals without changing geometry; the original native export remains unchanged. Final board assembly documentation is still a release task. No owner rerun is needed for this acceptance.

## Next functional simplification to evaluate

[Charger input gating](hardware/coupon/rev-a/charger-input-gating-assessment.md) could make the input-protection switch enforce Type-C permission, keeping the detector/logic upstream and the charger in fixed-current mode. This avoids a separate charger-mode actuator and PG receiver, but supply-domain changes, enable leakage/startup, voltage qualification and whole-port budgeting must be resolved together before an ADR/capture. The assessment provides a conditional enable-node budget and identifies why the current 10k RESET pull-up cannot be reused unchanged. A two-resistor U23 reuse screen for a whole-rail protector shows narrow illustrative DC margins; charger EN input current outside its 1.4 V test point and rail startup/transients remain unbounded. No circuit or user-facing requirement changed; no owner rerun is requested.

## Pack-current finding, 2026-09-25

[Candidate pack screen](docs/sourcing/pack-screen-2026-09-25.md) identifies a protected, NTC-equipped 700 mAh GlobTek pouch stocked by a US distributor and an 800 mAh version with its own fuel gauge. Both physically fit the rectangular envelope on paper. Their documented maximum charge currents of 700 mA and 400 mA are lower than the draft 872 mA ISET ceiling; neither can be substituted into the current charger design. The 700 mAh pack is at best a coupon candidate: the full-badge 2.49 W white-pattern model implies 0.83 A at 3.0 V, above its 0.70 A continuous discharge rating. Its drawing also needs exact-part and NTC curve confirmation. No pack is selected and no order is authorized.

The [charger thermal sensitivity screen](hardware/coupon/rev-a/charger-thermal-screen.md) shows 1.831 W idealized BQ24074 dissipation at the existing 0.872 A draft corner, 5.5 V charger IN and 3.4 V pack. The TI 44.5 °C/W reference-board figure predicts about 121.5 °C junction at an illustrative 40 °C local ambient, just below its 125 °C thermal-control point; actual compact PCB/enclosure resistance remains unknown. This is a calculated design risk, not a measured thermal result or a current-setting change.

## Current state

- 3.3 V converter capacitor checkpoint, 2026-09-30: Owner-supplied Murata SimSurfing CSV includes exact 22 µF input and 47 µF output parts. BQ24074 `OUT` regulates to at most 4.5 V in its specified steady state, while battery/standby modes feed OUT from the cell. Single-capacitor DC-bias plus illustrative tolerance/temperature calculations leave little aging margin. [ADR 0017](docs/decisions/0017-parallel-3v3-converter-capacitors.md) sets a **provisional coupon target** of two of each exact part in parallel. Manufacturer combined derating, charger OUT startup/transients and physical placement still gate selection. PWR-008 records the effective-capacitance and module-pad acceptance conditions. The historical unlinked nine-item converter candidate remains in `hardware/coupon/rev-a/staging/`; its native XML at c929711 confirmed 24 pin connections. A distinct, root-linked version with the physical-switch control pole passed [native review on 2026-10-05](docs/development/app-power-capture-review-2026-10-05.md). No physical board has been built.
- First-author passive-library review, 2026-09-30: owner-generated KiCad 10.0.6 bundle at `8014947` exported both Murata capacitor symbols, the new GRM21 footprint and previously staged Panasonic feedback symbols. [Review record](docs/development/3v3-passive-library-review-8014947.md) accepts the visible geometry and reports zero configured ERC and complete native XML for the **unchanged** staged circuit (400 PCB items / 1,507 logical pins). Exact packaging/order-code reconciliation, manufacturer combined derating, converter sheet, layout and Gate A remain open; no extra owner rerun is needed for this library checkpoint.

- Pack-selection checkpoint, 2026-09-27: [ADR 0016](docs/decisions/0016-runtime-and-fit-over-charge-speed.md) prioritizes fit and roughly six-hour runtime over the old fast-charge numbers. The [historical shortlist](docs/sourcing/pack-shortlist-2026-09-27.md) kept the documented 700 mAh GlobTek part as a conditional coupon-only candidate and the 900 mAh LiPol `LP452845` as a final-fit inquiry. Its 450 mA charge limit gives an ideal lower bound of 96 min to 80%; its continuous discharge rating and finished assembly dimensions remain unverified. ADR 0019 now supersedes that shortlist's three-wire requirement. No pack or ISET part selected; no battery order.

- Fuel-gauge decision, 2026-09-26: the owner accepted [ADR 0015](docs/decisions/0015-switch-fuel-gauge-with-application.md), disconnecting the MAX17048 from the protected cell with an independent latching-switch contact in OFF. The charger stays battery-connected for source-qualified OFF charging. PWR-003 remains <50 µA, without needing gauge firmware configuration before first battery insertion. OFF charging is not tracked by the gauge: post-ON SOC/runtime starts provisional until measured recovery is qualified. A [staged gauge sheet](hardware/coupon/rev-a/switch-gauge-boundary.md) contains the MAX17048, bypass and exact 2.2 kΩ Panasonic I²C pull-ups; its switched battery net is a **flagged draft source**, not a wired switch. The [native review at d9d717a](docs/development/gauge-review-d9d717a.md) accepts corrected rendering, zero configured ERC and full XML. Whole-bus timing and bench validation remain. Exact switch/pack/charger connection is not yet captured; PWR-003 is unverified.

- Independent layout feasibility checkpoint, 2026-09-26: the [front/rear bounding-box screen](mechanical/preliminary-placement-screen-2026-09-26.md) finds eight QT LED/USB courtyard overlaps on a centred 106 × 32.5 mm final-badge trial board. A 1.775 mm illustrative LED shift clears those *courtyard rectangles* by 0.25 mm. Rear MCU/three drivers and a 700 mAh coupon-only nominal pack have nonoverlapping trial rectangles, but the rest of the hardware, battery cables, RF, isolation and routing are not placed. This is not a KiCad PCB or final pack choice; complete schematic, board DRC and Gate A still gate fabrication.

- Requirements interview: complete.
- Architecture: accepted baseline, subject to coupon measurements.
- KiCad workflow: 10.0.6 stable baseline accepted; Coupon Rev A project and blank schematic scaffold created; the first macOS GUI round-trip opened and saved without errors, and CLI ERC reported zero violations.
- Coupon LED pair: `EAST10105RGBA0` in columns 0–7 and `QBLP1515A-RGB2A` in columns 8–15.
- Coupon LED libraries: first-author exact-MPN transcription and rendering review complete. Owner KiCad 10.0.6 exports at `27c01b4` passed pin/pad comparison; separate derived numbered views resolve body-outline/label overlap. The [review record](docs/development/led-library-review-27c01b4.md) preserves evidence and limits; independent Gate A verification remains pending.
- Coupon schematic: the matrix and TLC59581 driver passed owner KiCad 10.0.6 ERC/exported-netlist and six-page visual review at `8e95eb0`. Exact row-selection libraries passed native rendering review at `0c71860`; the complete row capture then passed zero-violation ERC, 335-item / 1,290-pin native connectivity and seven-page visual review at `eb4129b`. The exact N16R8 controller, reset/mode defaults, USB/UART boundaries and test pads passed the strict staged ERC gate, 356-item / 1,360-pin native connectivity, footprint render and eight-page visual review at `d56e1aa`. The [power pre-capture record](hardware/coupon/rev-a/power-pre-capture.md) freezes charger/current-limit and converter-divider arithmetic while keeping the USB default-current/data topology and pack-dependent NTC limits explicit. The [power-library audit](hardware/coupon/rev-a/power-library-audit.md) controls exact BQ25616J, TPS631000, TPS63020, USB-only LDO/inverter, TUSB320LAI, MAX17048, INA232 and USB ESD symbols/land patterns; corrected native rendering passed at `3638b1d`. The separately audited USB4505 candidate library passed host checks and [owner-generated native rendering review at `bf1627c`](docs/development/usb-connector-review-bf1627c.md). Input protection and remaining power circuits are uncaptured; the active USB interface increment is described below. 3.3 V N-MOS behavior plus hardware VLED inhibition remain explicit review/measurement items. See the [controller review](docs/development/controller-review-d56e1aa.md) and earlier capture/review records.
- Power-library review update: the native run at `c84f8ce` passed its staged electrical checks, but drawing/render review found a charger ground-pad short, wrong converter stencil geometry and overlapping symbol headings. The corrected native exports at `3638b1d` passed first-author review. The follow-on row layout and stale-note repairs passed native electrical and visual review at `91ef697`, closing the recorded first-author findings. PR #8 remains draft. The [finding record](docs/development/power-library-review-c84f8ce.md) also tracks the existing row-page title-block collision and stale annotations, now closed by the [native layout review](docs/development/layout-review-91ef697.md). See the [correction review](docs/development/power-library-review-3638b1d.md).
- USB/input closure: [ADR 0009](docs/decisions/0009-usb-input-current-closure.md) rejects the provisional direct BQ25616J ILIM network. [ADR 0010](docs/decisions/0010-source-qualified-off-charging.md) selects `BQ24074RGTR` + `BQ24392RSER` + `TS3USB31ERSER` + the audited `TUSB320LAIRWBR` for the next capture: fail-safe standby by default; autonomous OFF charging only from a positively classified charging source or Type-C 1.5 A/3 A source; SDP charging only while ON, configured and unsuspended. BQ24392 `GOOD_BAT` stays high with VBUS to avoid its finite dead-battery timer; the application-powered TS3USB31E supplies hard-OFF data isolation. The replacement libraries pass source/host audits and [native rendering review at c054cb4](docs/development/power-replacement-review-c054cb4.md). [ADR 0011](docs/decisions/0011-usb-total-current-headroom.md) corrects the configured-SDP current budget using low external ILIM plus a hardware-only resistor boost; the 1,024-case GPIO permission contract passes static checks. The permission gates and detector/data/LDO capture now exist; auxiliary-current proof, startup inhibition, thermal proof and remaining power capture are pending. See the [replacement-library audit](hardware/coupon/rev-a/power-replacement-library-audit.md), including the corrected unpublished geometry findings. The recovered USB4505 library and owner-generated KiCad 10.0.6 exports passed first-author review; cutout reliefs and stack-up/process qualification remain open.
- Repository workflow: owner granted standing permission on 2026-09-07 to merge PRs after applicable checks pass. LED library PR #2 through controller PR #7 are merged. Power/input is the active increment.
- Hardware testing: none.
- Native permission checkpoint: the owner-generated KiCad 10.0.6 bundle at `6d9a08b` passed first-author ERC/XML/render review: ten pages, 417 items / 1,536 logical pins and only the historical USB-boundary warning pair. See the [evidence record](docs/development/permission-review-6d9a08b.md). All seven new symbols and the corrected DBV5/DBV6 views passed; the supervisor was library-only at that checkpoint.
- USB interface checkpoint (2026-09-17): the [USB interface capture](hardware/coupon/rev-a/usb-interface-capture.md) connects the CC/BC detectors to the Schmitt logic, adds the connector/data path/ESD and USB-only LDO, and removes the old logic-supply flag. Source totals are eleven pages, 437 PCB items / 1,620 logical pin entries. Two exact Panasonic resistor symbols were added; no new footprint. The old USB ERC exceptions are retired: zero violations are required. Owner native review at `d502e65` passed zero-violation ERC and the complete XML; J1/U33 heading overlaps were found and source-corrected and closed by native review at `2bb0e08`. See the [review record](docs/development/usb-interface-review-d502e65.md). Connector VBUS and the draft +5V_USB source remain deliberately separate until input protection is designed. VBUS qualification, startup/ILIM actuation and the rest of the power section remain open.
- Logic-rail supervisor increment (2026-09-17): U34 TPS3808G01DBVR plus five passives now drives LOGIC_READY on the conditioning sheet; VBUS qualification and physical charger/ILIM inhibition remain open. Circuit totals: 443 items / 1,636 logical pins and eleven pages. [Static corner calculations and capture](hardware/coupon/rev-a/usb-supervision-capture.md) are recorded; [native review at `2bb0e08`](docs/development/logic-supervisor-review-2bb0e08.md) passed zero-violation ERC, complete XML and the supervisor/heading visual checks. The same record identifies a temperature-drift counterexample to the provisional ILIM current allocation; no current setting was raised.
- Current safe action: documentation, exact-part research, calculations and coupon design.
- Current stop condition: do not order a PCB or battery until the Gate A engineering review is complete.

- Programming-resistor increment (2026-09-17): [ADR 0012](docs/decisions/0012-programming-resistor-error-budget.md) selects three exact Panasonic ERA2AEB parts (0.1%, 25 ppm/K) while retaining ±1% total resistance error and unchanged current ceilings. Source-audited libraries now contain 45 symbols / 26 footprints; [native resistor rendering at `9e71bb5`](docs/development/precision-resistor-review-9e71bb5.md) passed. Assembly/service drift and actuator leakage still require qualification. No new circuit parts were placed. The next [actuator screening](hardware/coupon/rev-a/charger-actuator-screening.md) investigates ADG4612BCPZ-REEL7; the supplied PDF has now been visually reviewed. Its [candidate library audit](hardware/coupon/rev-a/charger-actuator-library-audit.md) adds one symbol and one project-derived footprint (46 symbols / 27 footprints total), with [native rendering at 2b7a468](docs/development/actuator-library-review-2b7a468.md) accepted. No actuator is selected or captured; intermediate-supply behavior, leakage, control loading and assembly qualification remain open.

## Non-negotiable constraints

| Area | Constraint |
|---|---|
| Matrix | 48 × 16 true RGB; pixel pitch must not exceed 1.95 mm |
| Size | Complete case no larger than 110 × 35 × 11 mm |
| Weight | Aim ≤75 g; never exceed 100 g including cell, case and magnets |
| Runtime | Roughly 6 h for the published reference workload; no automatic brightness reduction |
| Charging | USB-C at 5 V; correct A-to-C/C-to-C behaviour; charge while operating |
| Radio | BLE only in explicit programming mode |
| Controls | One momentary mode button and one latching on/off slide switch |
| OFF state | Application electronics, display and fuel gauge off; autonomous charging only from a hardware-qualified charging source (ADR 0015) |
| Assembly | Turnkey PCBA; user plugs in the protected battery and assembles the case |
| Quantity | Five assembled full badges after coupon validation |
| Budget | USD 500–800 for coupon, five badges, cells, basic test tools and shipping; case filament/design and independent review excluded |

## Accepted architecture baseline

- Three TLC59581 constant-current drivers, one per 16-column RGB block.
- Discrete four-pad common-anode RGB LEDs in a 1:16 multiplexed matrix.
- Coupon Rev A compares exact `EAST10105RGBA0` and `QBLP1515A-RGB2A` finalists at 1.95 mm pitch.
- The QBLP1515 coupon half preserves the manufacturer land pattern and alternates 0°/90° placement on a checkerboard under ADR 0008.
- Sixteen level-shifted P-channel MOSFET high-side row switches.
- ESP32-S3-WROOM-1U-N16R8 with an external 2.4 GHz FPC antenna.
- `BQ24074RGTR` standalone linear charger/PowerPath selected for capture, with thermal performance and exact pack current still requiring coupon and Gate A validation.
- `TUSB320LAIRWBR` Type-C current detection and application-powered `TS3USB31ERSER` hard-OFF data isolation. TPS70933DBVR supplies the USB-only logic domain. ADR 0013 removes BC1.2 detection and application charge grants; physical charger standby control remains uncaptured.
- TPS631000-class 3.3 V rail and TPS63020-class approximately 3.9 V LED rail.
- Switched MAX17048 fuel gauge, powering up afresh on each ON transition (ADR 0015). Battery current is measured externally during validation; no on-board INA232/shunt is populated (ADR 0021).
- Protected, keyed connectorized LiPo with hardware battery-facing NTC qualification; the sensor may be pack-integrated or PCB-mounted under ADR 0019. Capacity and exact pack remain open.
- KiCad 10.0.6 stable with project-local symbols, footprints and 3D models.

## Power states (ADRs 0013 and 0015)

| Switch | USB | Application/data | Charger input | Display |
|---|---|---|---|---|
| OFF | Absent | Off | Off | Off |
| OFF | USB-A/default/unclassified | Off | Standby | Off |
| OFF | Type-C 1.5 A/3 A | Off | Fixed-limit autonomous charging | Off |
| ON | Absent | Battery playback | Off | Fixed user brightness |
| ON | USB-A/default/unclassified | Battery operation; data if host present | Standby | Fixed user brightness |
| ON | Type-C 1.5 A/3 A | Operation; data if host present | Fixed-limit charge/PowerPath | Fixed user brightness |

These are required behaviors, not measured results. Unsupported-source USB recovery with a depleted or absent battery is not guaranteed.

## Development stages

1. **Documentation:** requirements, ADRs and candidate-part evidence.
2. **Coupon design:** production-intent 16 × 16 mixed-LED test board.
3. **Gate A review:** completed schematic plus preliminary layout reviewed independently.
4. **Coupon fabrication and bring-up:** five PCBs, three assembled.
5. **Gate B:** measured optical, electrical, thermal, runtime, RF and storage results.
6. **Full badge:** final six-layer PCB and enclosure.
7. **Gate C:** second review, frozen BOM and three comparable assembly quotes.
8. **Pilot:** five fully assembled badges.

## Open engineering decisions

- Project-local LED footprints plus pad, polarity, tape-orientation and optical-bin verification.
- Exact protected/terminated cell and connector.
- Confirm supplied TLC59581 RTQ0056E versus RTQ0056G package; qualify the nominal 4.85 mA current calculation and TI table discrepancies.
- BQ24074 fixed-current capture: permanent ILIM pair, ISET, termination, timer and exact-pack NTC network; input protection and physical standby control.
- Validation of Type-C advertisement changes, data isolation, reset/detach behavior and complete-port consumption under ADRs 0013/0014.
- Validation of the candidate `74HC4514PW,118`, `DMP2066LSN-7` and `2N7002K-7` row chain under real multiplex timing and current.
- Final USB ESD/VBUS protection topology.
- Final converter component values and layout.
- Coupon and final PCB stack-ups.
- Validation of the candidate external antenna's current gain documentation, case placement and worn RF performance.
- Winning LED, diffuser, current correction and GCLK timing after coupon tests.

## Language

- **Coupon:** the first 16 × 16 production-intent validation PCB.
- **Reference workload:** representative text/icons/animations with approximately 35% lit pixels at 25% fixed brightness.
- **Fixed brightness:** user-selected during programming; it is not changed automatically during playback.
- **Programming mode:** mode entered by holding the single button for about three seconds; BLE is enabled only in this state.
- **Release:** an immutable, hashed fabrication/assembly package tied to a tagged repository revision.

- Actuator supply analysis (2026-09-18): [conditional shared-rail calculation](hardware/coupon/rev-a/charger-actuator-supply-analysis.md) finds 0.2 V static UVLO margin, but does not close transient timing or control defaults. The ADG 17-ohm guarantee is restricted to its 4.5 V test envelope; no circuit capture or current-limit change.
