mulbc/rgb-badge/docs/development/vled-routing-trial-2026-10-06.md

<!-- SPDX-License-Identifier: CERN-OHL-S-2.0 -->

# Partial VLED routing study, 2026-10-06

The [standalone KiCad board](../../hardware/coupon/rev-a/staging/vled-routing-trial.kicad_pcb) adds twelve front-copper segments to the [13-footprint placement study](../../hardware/coupon/rev-a/staging/vled-layout-trial.kicad_pcb). [Its generator](../../tools/generate-vled-routing-trial.py) connects both IC pins for each inductor terminal, both input-capacitor positives to VIN, and the two closest output-capacitor positives to VOUT. It loads the actual schematic-net-assigned footprints and checks its copper anchor pads. Regeneration is byte-stable; board SHA-256: `a0c68c12ab34584cbf3b30aefdf774b87d43b270dab01499a8abf9b454d4a1b6`.

KiCad CLI 10.0.6's [raw native DRC report](vled-routing-drc-2026-10-06.json) shows **zero reported geometry violations and twenty unconnected items**. The previous unrouted version had thirty unconnected items. All routed segments are 0.20 mm wide and serve only to test connection and clearance geometry; no current capacity, switching performance or thermal margin is established. The board has no ground copper, feedback route, vias, interlock, LED load, other power stages or mechanical stack. It is not the coupon or final-board PCB. No physical hardware, firmware revision or measurement exists.

The initial positive-side paths can be drawn in this bay without native DRC conflicts. The next correction reorders `R84`/`R85`/`R86` within the same three 2 × 1 mm boxes, with each footprint rotated 180°. Native pad-coordinate inspection places R86's GND pad at (93.75, 23.30) mm, 3.042 mm in XY from U37's control-GND pad at (92.45, 26.05) mm; the original arrangement put that R86 pad at (99.05, 23.30) mm. R84's VLED pad is now near the outer output capacitor. This is an XY observation, not routed feedback or an electrical measurement. [TI's TPS63020 layout instructions](https://www.ti.com/lit/ds/symlink/tps63020.pdf#page=24) call for the feedback divider near control ground, short separated control-ground traces, and short/wide power and ground paths. Reserve those return paths and complete the divider, VINA and remaining output-capacitor routes before treating this as a converter layout candidate. The complete board must then receive routed DRC, thermal/current review and independent Gate A review before fabrication.
