mulbc/rgb-badge/docs/development/type-c-only-review-12a134f.md

<!-- SPDX-License-Identifier: CERN-OHL-S-2.0 -->

# Type-C-only native review at 12a134f

Reviewed 2026-09-19. Owner-generated KiCad 10.0.6 exports from `12a134f4614fc77316637105b76a50b6a3baa431`; first-author review, not independent Gate A.

## Evidence

| Artifact | SHA-256 |
|---|---|
| type-c-only-review-12a134f.zip | 3d758bd937fb2bceec46be88404eec90c384662e28991cd6dce6a601e68fa991 |
| coupon-schematic.pdf | 8c04b245152f2e3b9f1013169f60a4d71aebc15af53589a98ba31d22c5209086 |
| coupon-matrix.xml | 7930f5ef8454ad30c83eceb6c18951f495e50087ab0798ab7c2c771c5f05db50 |
| coupon-erc.rpt | bddde305323f8553b66fbfd9140acccecab6d33fa4b634466758907eadcfef0c |

The supplied terminal log identifies the source commit and reports successful ERC, XML and PDF export, with no subsequent git-status entries. ERC reports zero errors and zero warnings under the existing project configuration. It lists the existing ignored check categories (single-occurrence global labels, four-way junctions, SPICE models and footprint filters); no new exceptions were introduced by this fix.

The uploaded native XML was rerun through `tools/check-coupon-controller.py --netlist`: all 396 PCB items / 1,492 logical pins passed. This is native exported evidence, not the synthetic fixture.

## Visual review

Rendered and inspected PDF pages 9–11 (conditioning, permission and interface). No new overlaps, clipped labels or ambiguous drawn connections were found in these sheets. Page 9 shows TP21 on conditioned USB_OUT2, closing the isolated-label finding at cb81e86. Page 10 shows the reduced three-gate path and explicit test-output boundaries, with no switched ILIM branch. Page 11 shows the retained connector/ESD/CC detector, USB-only LDO and application-powered data isolator; connector VBUS and the staged protected supply remain explicitly separate. The large sheets have substantial whitespace after component removal; cosmetic repagination is deferred to avoid another low-value native checkpoint.

Unchanged pages and library geometry were not re-audited against manufacturer documents in this review. Their earlier records remain applicable only to unchanged content.

## Disposition

Accept the combined Type-C-only simplification checkpoint and close the prior OUT2 ERC finding. No source circuit changes are required from this review, and no user rerun is needed for this documentation update.

The power/input PR remains draft. Next functional work is protected input, VBUS qualification and physical charger standby/startup control, followed by charger/pack/NTC/timer/thermal and converter/gauge capture. A valid staged schematic does not establish complete power behavior, bench performance or fabrication readiness. Independent Gate A remains required.
