mulbc/rgb-badge/docs/decisions/0013-type-c-only-fixed-current-charging.md

<!-- SPDX-License-Identifier: CERN-OHL-S-2.0 -->

# ADR 0013: Type-C-only charging with one fixed input limit

- Status: Accepted by owner; capture and qualification pending
- Date: 2026-09-18
- Supersedes: ADRs 0010/0011 source policy and switched ILIM topology
- Retains: battery safeguards, current ceilings, OFF charging, operation while charging and independent Gate A

## Decision

Charge only when the Type-C source advertises 1.5 A or 3 A. USB-A connections and default-current Type-C connections do not power the system through the charger or charge the battery. Native USB data remains available while ON, with the application battery-powered when charging permission is absent. A depleted or missing battery is therefore not guaranteed to support USB recovery on an unsupported source.

Use one permanent resistor-programmed input-current limit, no switched parallel branch and no firmware charging grant. Keep BQ24074, TUSB320LAI, the USB-only logic supply and application-powered TS3USB31E isolation. Remove BQ24392 BC1.2 detection, its support parts and all BC/SDP/application-grant gates. ADG4612 is no longer needed for ILIM switching; its library remains historical candidate evidence only.

The current ceilings are not increased. Initially retain the already audited 3.65 kohm and 3.48 kohm precision resistors **permanently in parallel** as a single fixed setting: ideal calculated input range 0.834–0.975 A with the retained ±1% total resistance envelope. Two passive resistors avoid a new library/MPN review; there is no analog switch or intermediate node. A later single-resistor replacement requires its own value/tolerance check. ISET and battery prerequisites remain unchanged. The total-resistance qualification remains applicable, but switch leakage no longer contributes programming error.
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
