mulbc/rgb-badge/docs/development/actuator-library-review-2b7a468.md

<!-- SPDX-License-Identifier: CERN-OHL-S-2.0 -->

# Native actuator-library review: 2b7a468

Reviewed 2026-09-18. The candidate library rendering passes first-author review. This does not select the actuator, validate its circuit or authorize assembly.

The owner supplied `actuator-library-review-2b7a468.zip` and its KiCad 10.0.6 terminal transcript. This is the library-only source checkpoint `2b7a468b25b08fe40ad3fdfe2ccae62f4dab3cf3`.
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
