mulbc/rgb-badge/tools/check-power-libraries.py

#!/usr/bin/env python3
# SPDX-License-Identifier: Apache-2.0
"""Audit the controlled Coupon Rev A power/input component libraries.

This checks a controlled transcription of manufacturer pin tables and land
patterns. It does not approve the power architecture, schematic, PCB layout,
thermal design, assembly process or battery pack.
"""

from collections import Counter
from decimal import Decimal as D
from itertools import combinations
from pathlib import Path
import argparse
import runpy
import sys


LED = runpy.run_path(str(Path(__file__).with_name("check-led-libraries.py")))
parse, children, one = LED["parse_sexpr"], LED["children"], LED["only_child"]
property_map = LED["property_map"]
PROJECT = Path(__file__).resolve().parents[1] / "hardware" / "coupon" / "rev-a"
FP_PREFIX = "rgb-badge-coupon:"

PARTS = {
    "TPS259472ARPWR": {
        "footprint": "VQFN_TI_RPW0010A_2x2mm_HotRod",
        "datasheet": "https://www.ti.com/lit/ds/symlink/tps25947.pdf",
        "pins": {1: ("EN/UVLO", "input"), 2: ("OVCSEL", "input"),
                 3: ("PG", "open_collector"), 4: ("PGTH", "input"),
                 5: ("IN", "power_in"), 6: ("OUT", "power_out"),
                 7: ("DVDT", "output"), 8: ("GND", "power_in"),
                 9: ("ILM", "output"), 10: ("ITIMER", "output")},
    },
    "TPS259474ARPWR": {
        "footprint": "VQFN_TI_RPW0010A_2x2mm_HotRod",
        "datasheet": "https://www.ti.com/lit/ds/symlink/tps25947.pdf",
        "pins": {1: ("EN/UVLO", "input"), 2: ("OVLO", "input"),
                 3: ("PG", "open_collector"), 4: ("PGTH", "input"),
                 5: ("IN", "power_in"), 6: ("OUT", "power_out"),
                 7: ("DVDT", "output"), 8: ("GND", "power_in"),
                 9: ("ILM", "output"), 10: ("ITIMER", "output")},
    },
    "TPS70933DBVR": {
        "footprint": "SOT23_TI_DBV0005A",
        "datasheet": "https://www.ti.com/lit/ds/symlink/tps709.pdf",
        "pins": {1: ("IN", "power_in"), 2: ("GND", "power_in"),
                 3: ("EN", "input"), 4: ("NC", "passive"),
                 5: ("OUT", "power_out")},
    },
    "ADG4612BCPZ-REEL7": {
        "footprint": "LFCSP_ADI_CP16_22_3x3mm_P0.5mm_EP1.75mm",
        "datasheet": "https://www.analog.com/media/en/technical-documentation/data-sheets/ADG4612_4613.pdf",
        "pins": {0: ("GND_EP", "power_in"), 1: ("S1", "bidirectional"),
                 2: ("VSS", "power_in"), 3: ("GND", "power_in"),
                 4: ("S4", "bidirectional"), 5: ("D4", "bidirectional"),
                 6: ("IN4", "input"), 7: ("IN3", "input"),
                 8: ("D3", "bidirectional"), 9: ("S3", "bidirectional"),
                 10: ("NC", "passive"), 11: ("VDD", "power_in"),
                 12: ("S2", "bidirectional"), 13: ("D2", "bidirectional"),
                 14: ("IN2", "input"), 15: ("IN1", "input"),
                 16: ("D1", "bidirectional")},
    },
    "SN74LVC2G17DBVR": {
        "footprint": "SOT23_TI_DBV0006A",
        "datasheet": "https://www.ti.com/lit/ds/symlink/sn74lvc2g17.pdf",
        "pins": {1: ("1A", "input"), 2: ("GND", "power_in"), 3: ("2A", "input"),
                 4: ("2Y", "output"), 5: ("VCC", "power_in"), 6: ("1Y", "output")},
    },
    "SN74LVC1G00DBVR": {
        "footprint": "SOT23_TI_DBV0005A",
        "datasheet": "https://www.ti.com/lit/ds/symlink/sn74lvc1g00.pdf",
        "pins": {1: ("A", "input"), 2: ("B", "input"), 3: ("GND", "power_in"),
                 4: ("Y", "output"), 5: ("VCC", "power_in")},
    },
    "SN74LVC1G06DBVR": {
        "footprint": "SOT23_TI_DBV0005A",
        "datasheet": "https://www.ti.com/lit/ds/symlink/sn74lvc1g06.pdf",
        "pins": {1: ("NC", "passive"), 2: ("A", "input"), 3: ("GND", "power_in"),
                 4: ("Y", "open_collector"), 5: ("VCC", "power_in")},
    },
    "SN74LVC1G08DBVR": {
        "footprint": "SOT23_TI_DBV0005A",
        "datasheet": "https://www.ti.com/lit/ds/symlink/sn74lvc1g08.pdf",
        "pins": {1: ("A", "input"), 2: ("B", "input"), 3: ("GND", "power_in"),
                 4: ("Y", "output"), 5: ("VCC", "power_in")},
    },
    "SN74LVC1G11DBVR": {
        "footprint": "SOT23_TI_DBV0006A",
        "datasheet": "https://www.ti.com/lit/ds/symlink/sn74lvc1g11.pdf",
        "pins": {1: ("A", "input"), 2: ("GND", "power_in"), 3: ("B", "input"),
                 4: ("Y", "output"), 5: ("VCC", "power_in"), 6: ("C", "input")},
    },
    "SN74LVC1G32DBVR": {
        "footprint": "SOT23_TI_DBV0005A",
        "datasheet": "https://www.ti.com/lit/ds/symlink/sn74lvc1g32.pdf",
        "pins": {1: ("A", "input"), 2: ("B", "input"), 3: ("GND", "power_in"),
                 4: ("Y", "output"), 5: ("VCC", "power_in")},
    },
    "TPS3808G01DBVR": {
        "footprint": "SOT23_TI_DBV0006A",
        "datasheet": "https://www.ti.com/lit/ds/symlink/tps3808.pdf",
        "pins": {1: ("RESET", "open_collector"), 2: ("GND", "power_in"),
                 3: ("MR", "input"), 4: ("CT", "input"),
                 5: ("SENSE", "input"), 6: ("VDD", "power_in")},
    },
    "BQ24074RGTR": {
        "footprint": "VQFN_TI_RGT0016C_3x3mm_P0.5mm_EP1.68mm",
        "datasheet": "https://www.ti.com/lit/ds/symlink/bq24074.pdf",
        "pins": {
            1: ("TS", "input"), 2: ("BAT", "power_in"), 3: ("BAT", "power_in"),
            4: ("CE", "input"), 5: ("EN2", "input"), 6: ("EN1", "input"),
            7: ("PGOOD", "open_collector"), 8: ("VSS", "power_in"),
            9: ("CHG", "open_collector"), 10: ("OUT", "power_out"),
            11: ("OUT", "passive"), 12: ("ILIM", "input"), 13: ("IN", "power_in"),
            14: ("TMR", "input"), 15: ("ITERM", "input"), 16: ("ISET", "bidirectional"),
            17: ("VSS_EP", "power_in"),
        },
    },
    "BQ24392RSER": {
        "footprint": "UQFN_TI_RSE0010A_2x1.5mm_P0.5mm",
        "datasheet": "https://www.ti.com/lit/ds/symlink/bq24392.pdf",
        "pins": {
            1: ("SW_OPEN", "open_collector"), 2: ("DM_HOST", "bidirectional"),
            3: ("DP_HOST", "bidirectional"), 4: ("CHG_AL_N", "open_collector"),
            5: ("GOOD_BAT", "input"), 6: ("GND", "power_in"),
            7: ("DP_CON", "bidirectional"), 8: ("DM_CON", "bidirectional"),
            9: ("VBUS", "power_in"), 10: ("CHG_DET", "output"),
        },
    },
    "TS3USB31ERSER": {
        "footprint": "UQFN_TI_RSE0008A_1.5x1.5mm_P0.5mm",
        "datasheet": "https://www.ti.com/lit/ds/symlink/ts3usb31e.pdf",
        "pins": {
            1: ("OE", "input"), 2: ("HSD+", "bidirectional"),
            3: ("D+", "bidirectional"), 4: ("GND", "power_in"),
            5: ("D-", "bidirectional"), 6: ("HSD-", "bidirectional"),
            7: ("NC", "passive"), 8: ("VCC", "power_in"),
        },
    },
    "BQ25616JRTWT": {
        "footprint": "QFN_TI_RTW0024A_4x4mm_P0.5mm_EP2.7mm",
        "datasheet": "https://www.ti.com/lit/ds/symlink/bq25616.pdf",
        "pins": {
            1: ("VAC", "power_in"), 2: ("ACDRV", "output"),
            3: ("D+", "bidirectional"), 4: ("D-", "bidirectional"),
            5: ("STAT", "open_collector"), 6: ("OTG", "input"),
            7: ("PG", "open_collector"), 8: ("ILIM", "input"),
            9: ("CE", "input"), 10: ("ICHG", "input"),
            11: ("TS", "input"), 12: ("VSET", "input"),
            13: ("BAT", "power_in"), 14: ("BAT", "power_in"),
            15: ("SYS", "power_out"), 16: ("SYS", "power_out"),
            17: ("GND", "power_in"), 18: ("GND", "power_in"),
            19: ("SW", "passive"), 20: ("SW", "passive"),
            21: ("BTST", "passive"), 22: ("REGN", "power_out"),
            23: ("PMID", "power_out"), 24: ("VBUS", "power_in"),
            25: ("GND_EP", "power_in"),
        },
    },
    "TPS631000DRLR": {
        "footprint": "SOT5X3_TI_DRL0008A",
        "datasheet": "https://www.ti.com/lit/ds/symlink/tps631000.pdf",
        "pins": {
            1: ("VOUT", "power_out"), 2: ("LX2", "passive"),
            3: ("LX1", "passive"), 4: ("VIN", "power_in"),
            5: ("EN", "input"), 6: ("MODE", "input"),
            7: ("GND", "power_in"), 8: ("FB", "input"),
        },
    },
    "TLV75533PDBVR": {
        "footprint": "SOT23_TI_DBV0005A",
        "datasheet": "https://www.ti.com/lit/ds/symlink/tlv755p.pdf",
        "pins": {
            1: ("IN", "power_in"), 2: ("GND", "power_in"),
            3: ("EN", "input"), 4: ("NC", "passive"),
            5: ("OUT", "power_out"),
        },
    },
    "SN74LVC1G04DBVR": {
        "footprint": "SOT23_TI_DBV0005A",
        "datasheet": "https://www.ti.com/lit/ds/symlink/sn74lvc1g04.pdf",
        "pins": {
            1: ("NC", "passive"), 2: ("A", "input"),
            3: ("GND", "power_in"), 4: ("Y", "output"),
            5: ("VCC", "power_in"),
        },
    },
    "INA232AIDDFR": {
        "footprint": "SOT23_THIN_TI_DDF0008A",
        "datasheet": "https://www.ti.com/lit/ds/symlink/ina232.pdf",
        "pins": {
            1: ("IN+", "input"), 2: ("IN-", "input"),
            3: ("GND", "power_in"), 4: ("VS", "power_in"),
            5: ("SCL", "input"), 6: ("SDA", "bidirectional"),
            7: ("A0", "input"), 8: ("ALERT", "open_collector"),
        },
    },
    "TPD4E05U06DQAR": {
        "footprint": "USON_TI_DQA0010A",
        "datasheet": "https://www.ti.com/lit/ds/symlink/tpd4e05u06.pdf",
        "pins": {
            1: ("D1+", "passive"), 2: ("D1-", "passive"),
            3: ("GND", "power_in"), 4: ("D2+", "passive"),
            5: ("D2-", "passive"), 6: ("NC", "passive"),
            7: ("NC", "passive"), 8: ("GND", "power_in"),
            9: ("NC", "passive"), 10: ("NC", "passive"),
        },
    },
    "TUSB320LAIRWBR": {
        "footprint": "X2QFN_TI_RWB0012A_1.6x1.6mm_P0.4mm",
        "datasheet": "https://www.ti.com/lit/ds/symlink/tusb320lai.pdf",
        "pins": {
            1: ("CC1", "bidirectional"), 2: ("CC2", "bidirectional"),
            3: ("PORT", "input"), 4: ("VBUS_DET", "input"),
            5: ("ADDR", "input"), 6: ("INT_N/OUT3", "open_collector"),
            7: ("SDA/OUT1", "bidirectional"), 8: ("SCL/OUT2", "bidirectional"),
            9: ("ID", "open_collector"), 10: ("GND", "power_in"),
            11: ("EN_N", "input"), 12: ("VDD", "power_in"),
        },
    },
    "TPS63020DSJT": {
        "footprint": "VSON_TI_DSJ0014_4x3mm_P0.5mm_EP2.85x1.58mm",
        "datasheet": "https://www.ti.com/lit/ds/symlink/tps63020.pdf",
        "pins": {
            1: ("VINA", "power_in"), 2: ("GND", "power_in"),
            3: ("FB", "input"), 4: ("VOUT", "power_out"),
            # One common VOUT pin is passive in ERC to avoid connecting
            # two power-output symbols on the same physical output rail.
            5: ("VOUT", "passive"), 6: ("L2", "passive"),
            7: ("L2", "passive"), 8: ("L1", "passive"),
            9: ("L1", "passive"), 10: ("VIN", "power_in"),
            11: ("VIN", "power_in"), 12: ("EN", "input"),
            13: ("PS/SYNC", "input"), 14: ("PG", "open_collector"),
            15: ("PGND_EP", "power_in"),
        },
    },
    "MAX17048G+T10": {
        "footprint": "TDFN_Maxim_T822-3_2x2mm_P0.5mm_EP0.7x1.38mm",
        "datasheet": "https://www.analog.com/media/en/technical-documentation/data-sheets/MAX17048-MAX17049.pdf",
        "pins": {
            1: ("CTG", "power_in"), 2: ("CELL", "passive"),
            3: ("VDD", "power_in"), 4: ("GND", "power_in"),
            5: ("ALRT", "open_collector"), 6: ("QSTRT", "input"),
            7: ("SCL", "input"), 8: ("SDA", "bidirectional"),
            9: ("GND_EP", "power_in"),
        },
    },
}


def require(condition, message):
    if not condition:
        raise ValueError(message)


def library_pins(symbol):
    result = {}
    for unit in children(symbol, "symbol"):
        for pin in children(unit, "pin"):
            number = one(pin, "number", "pin")[1]
            require(number not in result, f"duplicate library pin {number}")
            result[number] = pin
    return result


def footprint(project, name):
    path = project / "footprints" / "rgb-badge-coupon.pretty" / f"{name}.kicad_mod"
    return parse(path)


def dec(values):
    return tuple(map(D, values))


def pad_position(pad):
    return dec(one(pad, "at", "pad")[1:3])


def pad_size(pad):
    return dec(one(pad, "size", "pad")[1:])


def pad_layers(pad):
    return one(pad, "layers", "pad")[1:]


def check_copper_separation(root):
    """Conservative bounding-box check, independent of the dimension audit.

    Only current unrotated rectangular/rounded lands are supported. Same-number
    thermal fingers may intentionally meet. This is not board-level KiCad DRC.
    """
    pads = [p for p in children(root, "pad") if "F.Cu" in pad_layers(p)]
    for pad in pads:
        require(pad[1] and pad[3] in ("rect", "roundrect"),
                f"{root[1]}: unsupported copper pad geometry")
        at = one(pad, "at", "pad")
        require(len(at) == 3 or D(at[3]) == 0,
                f"{root[1]}: rotated copper pad needs a geometry-aware check")
    for a, b in combinations(pads, 2):
        if a[1] == b[1]:
            continue
        ap, bp = pad_position(a), pad_position(b)
        az, bz = pad_size(a), pad_size(b)
        gaps = [abs(ap[i] - bp[i]) - (az[i] + bz[i]) / 2 for i in (0, 1)]
        require(max(gaps) > 0,
                f"{root[1]}: copper pads {a[1]}/{b[1]} touch or overlap in bounding boxes")


def check_symbol_header_clearance(symbol):
    """Reserve a full text-height above top-facing pin endpoints."""
    pins = library_pins(symbol)
    top = [D(one(p, "at", "pin")[2]) for p in pins.values()
           if D(one(p, "at", "pin")[3]) == 270]
    if not top:
        return
    fields = {p[1]: p for p in children(symbol, "property")}
    value = fields["Value"]
    height = D(one(one(one(value, "effects", "value"), "font", "font"), "size", "font")[2])
    value_y = D(one(value, "at", "value")[2])
    reference_y = D(one(fields["Reference"], "at", "reference")[2])
    require(value_y - height / 2 >= max(top) + height,
            f"{symbol[1]}: header overlaps top-pin keepout")
    require(reference_y - value_y >= 2 * height,
            f"{symbol[1]}: reference/value header spacing too small")


def check_symbol_libraries(project):
    library = parse(project / "symbols" / "rgb-badge-coupon.kicad_sym")
    symbols = {symbol[1]: symbol for symbol in children(library, "symbol")}
    for mpn, audit in PARTS.items():
        require(mpn in symbols, f"missing exact power symbol {mpn}")
        symbol = symbols[mpn]
        properties = property_map(symbol)
        require(properties.get("MPN") == mpn, f"{mpn}: MPN property mismatch")
        require(properties.get("Footprint") == FP_PREFIX + audit["footprint"],
                f"{mpn}: footprint property mismatch")
        require(properties.get("Datasheet") == audit["datasheet"],
                f"{mpn}: datasheet property mismatch")
        pins = library_pins(symbol)
        check_symbol_header_clearance(symbol)
        require(set(pins) == set(map(str, audit["pins"])), f"{mpn}: pin numbers mismatch")
        for number, (name, electrical_type) in audit["pins"].items():
            pin = pins[str(number)]
            require(one(pin, "name", f"{mpn}.{number}")[1] == name,
                    f"{mpn}.{number}: pin name mismatch")
            require(pin[1] == electrical_type, f"{mpn}.{number}: electrical type mismatch")
    require(library_pins(symbols["BQ25616JRTWT"])["9"][2] == "inverted",
            "BQ25616J CE must show active-low inversion")
    for mpn, number in (("BQ24074RGTR", "4"), ("BQ24392RSER", "4"),
                        ("TS3USB31ERSER", "1")):
        require(library_pins(symbols[mpn])[number][2] == "inverted",
                f"{mpn}.{number} must show active-low inversion")
    require(library_pins(symbols["SN74LVC1G04DBVR"])["4"][2] == "inverted",
            "SN74LVC1G04 output must show inversion")
    require(library_pins(symbols["TUSB320LAIRWBR"])["11"][2] == "inverted",
            "TUSB320LAI EN_N must show active-low inversion")
    for mpn in ("SN74LVC1G00DBVR", "SN74LVC1G06DBVR", "SN74LVC1G08DBVR",
                "SN74LVC1G11DBVR", "SN74LVC1G32DBVR"):
        expected = "inverted" if mpn in ("SN74LVC1G00DBVR", "SN74LVC1G06DBVR") else "line"
        require(library_pins(symbols[mpn])["4"][2] == expected,
                f"{mpn}: output inversion mismatch")
    for number in ("1", "3"):
        require(library_pins(symbols["TPS3808G01DBVR"])[number][2] == "inverted",
                f"TPS3808G01DBVR.{number} must show active-low inversion")
    for number in ("4", "6"):
        require(library_pins(symbols["SN74LVC2G17DBVR"])[number][2] == "line",
                f"SN74LVC2G17DBVR.{number}: non-inverting buffer output required")
    adg = symbols["ADG4612BCPZ-REEL7"]
    require(property_map(adg).get("Manufacturer") == "Analog Devices", "ADG manufacturer mismatch")
    for number in ("6", "7", "14", "15"):
        require(library_pins(adg)[number][2] == "line", "ADG4612 controls must be active high")
    return symbols


def check_rtw_footprint(project):
    root = footprint(project, "QFN_TI_RTW0024A_4x4mm_P0.5mm_EP2.7mm")
    pads = children(root, "pad")
    numbered = {pad[1]: pad for pad in pads if pad[1]}
    require(set(numbered) == set(map(str, range(1, 26))), "RTW pad numbers mismatch")
    for number in range(1, 25):
        pad = numbered[str(number)]
        if number <= 6:
            position = (D("-1.975"), D("-1.25") + D("0.5") * (number - 1))
            size = (D("0.85"), D("0.28"))
        elif number <= 12:
            position = (D("-1.25") + D("0.5") * (number - 7), D("1.975"))
            size = (D("0.28"), D("0.85"))
        elif number <= 18:
            position = (D("1.975"), D("1.25") - D("0.5") * (number - 13))
            size = (D("0.85"), D("0.28"))
        else:
            position = (D("1.25") - D("0.5") * (number - 19), D("-1.975"))
            size = (D("0.28"), D("0.85"))
        require(pad_position(pad) == position, f"RTW pad {number} position mismatch")
        require(pad_size(pad) == size, f"RTW pad {number} size mismatch")
        require(pad_layers(pad) == ["F.Cu", "F.Paste", "F.Mask"],
                f"RTW pad {number} layer mismatch")
        require(D(one(pad, "solder_paste_margin", "RTW pad")[1]) == D("-0.025"),
                f"RTW pad {number} signal paste reduction mismatch")
        require(D(one(pad, "solder_mask_margin", "RTW pad")[1]) == D("0.07"),
                f"RTW pad {number} mask margin mismatch")
        require(D(one(pad, "roundrect_rratio", "RTW pad")[1]) == D("0.5"),
                f"RTW pad {number} corner radius mismatch")
    ep = numbered["25"]
    require(pad_position(ep) == (D("0"), D("0")), "RTW exposed-pad position mismatch")
    require(pad_size(ep) == (D("2.7"), D("2.7")), "RTW exposed-pad size mismatch")
    require(pad_layers(ep) == ["F.Cu", "F.Mask"], "RTW exposed-pad layers mismatch")
    paste = [pad for pad in pads if not pad[1]]
    require(len(paste) == 4, "RTW stencil aperture count mismatch")
    require({pad_position(pad) for pad in paste} == {
        (D("-0.7"), D("-0.7")), (D("0.7"), D("-0.7")),
        (D("-0.7"), D("0.7")), (D("0.7"), D("0.7")),
    }, "RTW stencil aperture positions mismatch")
    require(all(pad_size(pad) == (D("1.1"), D("1.1")) for pad in paste),
            "RTW stencil aperture size mismatch")
    require(all(pad_layers(pad) == ["F.Paste"] for pad in paste),
            "RTW stencil aperture layers mismatch")
    marker = one(root, "fp_circle", "RTW pin-1 marker")
    require(dec(one(marker, "center", "RTW pin-1 marker")[1:]) == (D("-2.45"), D("-1.65")),
            "RTW pin-1 marker mismatch")


def check_replacement_geometry(root, body, courtyard, marker):
    """Also guard radius and outline errors invisible to the pad-size tables."""
    require(D(one(root, "solder_mask_margin", "footprint")[1]) == D("0.05"),
            f"{root[1]} mask margin mismatch")
    for pad in children(root, "pad"):
        require(pad[3] == "roundrect", f"{root[1]} pad shape mismatch")
        radius = min(pad_size(pad)) * D(one(pad, "roundrect_rratio", "pad")[1])
        require(abs(radius - D("0.05")) <= D("0.000001"),
                f"{root[1]} pad {pad[1]} corner radius mismatch")
        for override in ("solder_mask_margin", "solder_paste_margin",
                         "solder_paste_margin_ratio"):
            require(not children(pad, override), f"{root[1]} unexpected pad {override}")
    for override in ("solder_paste_margin", "solder_paste_margin_ratio"):
        require(not children(root, override), f"{root[1]} unexpected footprint {override}")
    for layer, extent in (("F.Fab", body), ("F.CrtYd", courtyard)):
        rectangles = [r for r in children(root, "fp_rect")
                      if one(r, "layer", "rectangle")[1] == layer]
        require(len(rectangles) == 1, f"{root[1]} {layer} outline count mismatch")
        require(dec(one(rectangles[0], "start", "rectangle")[1:]) == tuple(-v for v in dec(extent))
                and dec(one(rectangles[0], "end", "rectangle")[1:]) == dec(extent),
                f"{root[1]} {layer} outline mismatch")
    circle = one(root, "fp_circle", "pin-1 marker")
    require(dec(one(circle, "center", "circle")[1:]) == dec(marker)
            and one(circle, "layer", "circle")[1] == "F.SilkS",
            f"{root[1]} pin-1 marker mismatch")


def check_rgt_footprint(project):
    root = footprint(project, PARTS["BQ24074RGTR"]["footprint"])
    pads = children(root, "pad")
    require(Counter(p[1] for p in pads) == Counter([*map(str, range(1, 18)), ""]),
            "RGT0016C pad numbers mismatch")
    numbered = {p[1]: p for p in pads}
    for number in range(1, 17):
        j = (number - 1) % 4
        if number <= 4:
            position, size = (D("-1.4"), D("-0.75") + D("0.5") * j), dec(("0.6", "0.24"))
        elif number <= 8:
            position, size = (D("-0.75") + D("0.5") * j, D("1.4")), dec(("0.24", "0.6"))
        elif number <= 12:
            position, size = (D("1.4"), D("0.75") - D("0.5") * j), dec(("0.6", "0.24"))
        else:
            position, size = (D("0.75") - D("0.5") * j, D("-1.4")), dec(("0.24", "0.6"))
        pad = numbered[str(number)]
        require(pad_position(pad) == position, f"RGT0016C pad {number} position mismatch")
        require(pad_size(pad) == size, f"RGT0016C pad {number} size mismatch")
        require(pad_layers(pad) == ["F.Cu", "F.Paste", "F.Mask"],
                f"RGT0016C pad {number} layers mismatch")
    for number, size, layers in (("17", "1.68", ["F.Cu", "F.Mask"]),
                                  ("", "1.55", ["F.Paste"])):
        pad = numbered[number]
        require(pad_position(pad) == dec(("0", "0")), "RGT0016C central pad position mismatch")
        require(pad_size(pad) == (D(size), D(size)), "RGT0016C central pad size mismatch")
        require(pad_layers(pad) == layers, "RGT0016C central pad layers mismatch")
    require(D("0.84") < D("1.55") ** 2 / D("1.68") ** 2 < D("0.86"),
            "RGT0016C stencil coverage mismatch")
    check_replacement_geometry(root, ("1.5", "1.5"), ("1.95", "1.95"), ("-2.12", "-1.25"))


def check_rse_footprint(project, mpn, positions, narrow, end, body, courtyard, marker):
    root = footprint(project, PARTS[mpn]["footprint"])
    pads = children(root, "pad")
    require(Counter(p[1] for p in pads) == Counter(positions.keys()), f"{mpn} pad numbers mismatch")
    for pad in pads:
        number = pad[1]
        size = ("0.3", "0.6") if number in end else ("0.55", "0.2" if number in narrow else "0.25")
        require(pad_position(pad) == dec(positions[number]), f"{mpn} pad {number} position mismatch")
        require(pad_size(pad) == dec(size), f"{mpn} pad {number} size mismatch")
        require(pad_layers(pad) == ["F.Cu", "F.Paste", "F.Mask"], f"{mpn} pad {number} layers mismatch")
    check_replacement_geometry(root, body, courtyard, marker)


def check_rse_footprints(project):
    check_rse_footprint(project, "BQ24392RSER", {
        "1": ("-0.675", "-0.75"), "2": ("-0.675", "-0.25"),
        "3": ("-0.675", "0.25"), "4": ("-0.675", "0.75"), "5": ("0", "0.9"),
        "6": ("0.675", "0.75"), "7": ("0.675", "0.25"),
        "8": ("0.675", "-0.25"), "9": ("0.675", "-0.75"), "10": ("0", "-0.9"),
    }, {"2", "3", "7", "8"}, {"5", "10"}, ("0.75", "1"), ("1.2", "1.45"), ("-1.42", "-0.95"))
    check_rse_footprint(project, "TS3USB31ERSER", {
        "1": ("-0.675", "-0.5"), "2": ("-0.675", "0"), "3": ("-0.675", "0.5"),
        "4": ("0", "0.65"), "5": ("0.675", "0.5"), "6": ("0.675", "0"),
        "7": ("0.675", "-0.5"), "8": ("0", "-0.65"),
    }, {"2", "6"}, {"4", "8"}, ("0.75", "0.75"), ("1.2", "1.2"), ("-1.42", "-0.75"))


def check_drl_footprint(project):
    root = footprint(project, "SOT5X3_TI_DRL0008A")
    pads = children(root, "pad")
    require(Counter(pad[1] for pad in pads) == Counter(map(str, range(1, 9))),
            "DRL pad numbers mismatch")
    by_number = {pad[1]: pad for pad in pads}
    for number in range(1, 9):
        if number <= 4:
            position = (D("-0.74"), D("-0.75") + D("0.5") * (number - 1))
        else:
            position = (D("0.74"), D("0.75") - D("0.5") * (number - 5))
        pad = by_number[str(number)]
        require(pad_position(pad) == position, f"DRL pad {number} position mismatch")
        require(pad_size(pad) == (D("0.67"), D("0.3")), f"DRL pad {number} size mismatch")
        require(pad_layers(pad) == ["F.Cu", "F.Paste", "F.Mask"],
                f"DRL pad {number} layer mismatch")
    marker = one(root, "fp_circle", "DRL pin-1 marker")
    require(dec(one(marker, "center", "DRL pin-1 marker")[1:]) == (D("-1.25"), D("-1.20")),
            "DRL pin-1 marker mismatch")


def check_simple_gullwing(project, name, expected_positions, expected_size, marker_position):
    root = footprint(project, name)
    pads = children(root, "pad")
    require(Counter(pad[1] for pad in pads) == Counter(expected_positions.keys()),
            f"{name} pad numbers mismatch")
    by_number = {pad[1]: pad for pad in pads}
    for number, position in expected_positions.items():
        pad = by_number[number]
        require(pad_position(pad) == dec(position), f"{name} pad {number} position mismatch")
        require(pad_size(pad) == dec(expected_size), f"{name} pad {number} size mismatch")
        require(pad_layers(pad) == ["F.Cu", "F.Paste", "F.Mask"],
                f"{name} pad {number} layer mismatch")
    marker = one(root, "fp_circle", f"{name} pin-1 marker")
    require(dec(one(marker, "center", f"{name} pin-1 marker")[1:]) == dec(marker_position),
            f"{name} pin-1 marker mismatch")


def check_phase_two_footprints(project):
    check_simple_gullwing(project, "SOT23_TI_DBV0005A", {
        "1": ("-1.3", "-0.95"), "2": ("-1.3", "0"), "3": ("-1.3", "0.95"),
        "4": ("1.3", "0.95"), "5": ("1.3", "-0.95"),
    }, ("1.1", "0.6"), ("-2.05", "-1.45"))
    check_simple_gullwing(project, "SOT23_TI_DBV0006A", {
        "1": ("-1.3", "-0.95"), "2": ("-1.3", "0"), "3": ("-1.3", "0.95"),
        "4": ("1.3", "0.95"), "5": ("1.3", "0"), "6": ("1.3", "-0.95"),
    }, ("1.1", "0.6"), ("-2.05", "-1.45"))
    for name in ("SOT23_TI_DBV0005A", "SOT23_TI_DBV0006A"):
        root = footprint(project, name)
        for layer, start, end in (("F.Fab", ("-0.8", "-1.45"), ("0.8", "1.45")),
                                  ("F.CrtYd", ("-2.15", "-1.8"), ("2.15", "1.8"))):
            rects = [r for r in children(root, "fp_rect") if one(r, "layer", name)[1] == layer]
            require(len(rects) == 1, f"{name}: {layer} rectangle count mismatch")
            require(dec(one(rects[0], "start", name)[1:]) == dec(start) and
                    dec(one(rects[0], "end", name)[1:]) == dec(end),
                    f"{name}: {layer} outline mismatch")
        for pad in children(root, "pad"):
            radius = D(one(pad, "roundrect_rratio", name)[1]) * min(pad_size(pad))
            require(pad[2:4] == ["smd", "roundrect"] and abs(radius - D("0.05")) < D("0.0001"),
                    f"{name}: pad corner radius mismatch")
        if name == "SOT23_TI_DBV0006A":
            require(one(root, "solder_mask_margin", name)[1] == "0.05",
                    f"{name}: mask margin mismatch")
            require(one(root, "solder_paste_margin", name)[1] == "0" and
                    one(root, "solder_paste_ratio", name)[1] == "0",
                    f"{name}: stencil margin mismatch")
    check_simple_gullwing(project, "SOT23_THIN_TI_DDF0008A", {
        "1": ("-1.3", "-0.975"), "2": ("-1.3", "-0.325"),
        "3": ("-1.3", "0.325"), "4": ("-1.3", "0.975"),
        "5": ("1.3", "0.975"), "6": ("1.3", "0.325"),
        "7": ("1.3", "-0.325"), "8": ("1.3", "-0.975"),
    }, ("1.05", "0.45"), ("-2.05", "-1.45"))

    root = footprint(project, "USON_TI_DQA0010A")
    pads = children(root, "pad")
    require(Counter(pad[1] for pad in pads) == Counter(map(str, range(1, 11))),
            "DQA0010A pad numbers mismatch")
    by_number = {pad[1]: pad for pad in pads}
    for number in range(1, 11):
        if number <= 5:
            position = (D("-0.4175"), D("-1.0") + D("0.5") * (number - 1))
        else:
            position = (D("0.4175"), D("1.0") - D("0.5") * (number - 6))
        pad = by_number[str(number)]
        size = (D("0.565"), D("0.4") if number in (3, 8) else D("0.2"))
        require(pad_position(pad) == position, f"DQA0010A pad {number} position mismatch")
        require(pad_size(pad) == size, f"DQA0010A pad {number} size mismatch")
        require(pad_layers(pad) == ["F.Cu", "F.Paste", "F.Mask"],
                f"DQA0010A pad {number} layer mismatch")
    marker = one(root, "fp_circle", "DQA0010A pin-1 marker")
    require(dec(one(marker, "center", "DQA0010A pin-1 marker")[1:]) ==
            (D("-0.95"), D("-1.35")), "DQA0010A pin-1 marker mismatch")


def check_rwb_footprint(project):
    root = footprint(project, "X2QFN_TI_RWB0012A_1.6x1.6mm_P0.4mm")
    pads = children(root, "pad")
    numbered = {pad[1]: pad for pad in pads if pad[1]}
    require(set(numbered) == set(map(str, range(1, 13))), "RWB0012A pad numbers mismatch")
    positions = {
        "1": ("-0.65", "-0.20"), "2": ("-0.65", "0.20"),
        "3": ("-0.60", "0.75"), "4": ("-0.20", "0.75"),
        "5": ("0.20", "0.75"), "6": ("0.60", "0.75"),
        "7": ("0.65", "0.20"), "8": ("0.65", "-0.20"),
        "9": ("0.60", "-0.75"), "10": ("0.20", "-0.75"),
        "11": ("-0.20", "-0.75"), "12": ("-0.60", "-0.75"),
    }
    side_numbers = {"1", "2", "7", "8"}
    for number, position in positions.items():
        pad = numbered[number]
        require(pad_position(pad) == dec(position), f"RWB0012A pad {number} position mismatch")
        size = (D("0.70"), D("0.20")) if number in side_numbers else (D("0.20"), D("0.50"))
        require(pad_size(pad) == size, f"RWB0012A pad {number} size mismatch")
        layers = ["F.Cu", "F.Mask"] if number in side_numbers else ["F.Cu", "F.Paste", "F.Mask"]
        require(pad_layers(pad) == layers, f"RWB0012A pad {number} layer mismatch")
    paste = [pad for pad in pads if not pad[1]]
    require(len(paste) == 4, "RWB0012A side stencil aperture count mismatch")
    require({pad_position(pad) for pad in paste} == {
        (D("-0.65"), D("-0.20")), (D("-0.65"), D("0.20")),
        (D("0.65"), D("0.20")), (D("0.65"), D("-0.20")),
    }, "RWB0012A side stencil aperture positions mismatch")
    require(all(pad_size(pad) == (D("0.67"), D("0.20")) for pad in paste),
            "RWB0012A side stencil aperture size mismatch")
    require(all(pad_layers(pad) == ["F.Paste"] for pad in paste),
            "RWB0012A side stencil aperture layers mismatch")
    marker = one(root, "fp_circle", "RWB0012A pin-1 marker")
    require(dec(one(marker, "center", "RWB0012A pin-1 marker")[1:]) ==
            (D("-1.25"), D("-0.75")), "RWB0012A pin-1 marker mismatch")


def check_dsj_footprint(project):
    root = footprint(project, "VSON_TI_DSJ0014_4x3mm_P0.5mm_EP2.85x1.58mm")
    pads = children(root, "pad")
    signal = {pad[1]: pad for pad in pads if pad[1] and pad[1] != "15"}
    require(set(signal) == set(map(str, range(1, 15))), "DSJ0014 signal pad numbers mismatch")
    for number in range(1, 15):
        if number <= 7:
            position = (D("-1.50") + D("0.50") * (number - 1), D("-1.40"))
        else:
            position = (D("1.50") - D("0.50") * (number - 8), D("1.40"))
        pad = signal[str(number)]
        require(pad_position(pad) == position, f"DSJ0014 pad {number} position mismatch")
        require(pad_size(pad) == (D("0.24"), D("0.60")),
                f"DSJ0014 pad {number} size mismatch")
        require(pad_layers(pad) == ["F.Cu", "F.Paste", "F.Mask"],
                f"DSJ0014 pad {number} layer mismatch")
        mask_margin = one(pad, "solder_mask_margin", f"DSJ0014 pad {number}")
        require(D(mask_margin[1]) == D("0.07"),
                f"DSJ0014 pad {number} solder-mask margin mismatch")

    thermal = [pad for pad in pads if pad[1] == "15"]
    require(len(thermal) == 9, "DSJ0014 exposed copper piece count mismatch")
    central = [pad for pad in thermal if pad_position(pad) == (D("0"), D("0"))]
    require(len(central) == 1, "DSJ0014 central exposed pad mismatch")
    require(pad_size(central[0]) == (D("2.85"), D("1.58")),
            "DSJ0014 central exposed pad size mismatch")
    fingers = [pad for pad in thermal if pad is not central[0]]
    require({pad_position(pad) for pad in fingers} == {
        (x, y) for x in (D("-1.8125"), D("1.8125"))
        for y in (D("-0.69"), D("-0.23"), D("0.23"), D("0.69"))
    }, "DSJ0014 thermal-finger positions mismatch")
    require(all(pad_size(pad) == (D("0.775"), D("0.20")) for pad in fingers),
            "DSJ0014 thermal-finger size mismatch")
    require(all(pad_layers(pad) == ["F.Cu", "F.Mask"] for pad in thermal),
            "DSJ0014 exposed copper layers mismatch")

    paste = [pad for pad in pads if not pad[1]]
    require(len(paste) == 12, "DSJ0014 thermal stencil aperture count mismatch")
    central_paste = [pad for pad in paste if pad_size(pad) == (D("1.25"), D("0.66"))]
    require({pad_position(pad) for pad in central_paste} == {
        (D("-0.725"), D("-0.46")), (D("0.725"), D("-0.46")),
        (D("-0.725"), D("0.46")), (D("0.725"), D("0.46")),
    }, "DSJ0014 central stencil positions mismatch")
    side_paste = [pad for pad in paste if pad_size(pad) == (D("0.85"), D("0.20"))]
    require({pad_position(pad) for pad in side_paste} == {
        (x, y) for x in (D("-1.775"), D("1.775"))
        for y in (D("-0.69"), D("-0.23"), D("0.23"), D("0.69"))
    }, "DSJ0014 side stencil positions mismatch")
    require(len(central_paste) == 4 and len(side_paste) == 8,
            "DSJ0014 thermal stencil aperture sizes mismatch")
    require(all(pad[3] == "rect" for pad in paste), "DSJ0014 thermal stencil shape mismatch")
    # These rectangles share edges, not area: their sum equals the union area.
    # An independent coverage sanity check catches a swapped 0.46/0.66 dimension.
    copper_area = sum(pad_size(p)[0] * pad_size(p)[1] for p in thermal)
    paste_area = sum(pad_size(p)[0] * pad_size(p)[1] for p in paste)
    require(D("0.80") < paste_area / copper_area < D("0.82"),
            "DSJ0014 thermal paste coverage is not approximately 81 percent")
    require(all(pad_layers(pad) == ["F.Paste"] for pad in paste),
            "DSJ0014 thermal stencil aperture layers mismatch")
    marker = one(root, "fp_circle", "DSJ0014 pin-1 marker")
    require(dec(one(marker, "center", "DSJ0014 pin-1 marker")[1:]) ==
            (D("-2.50"), D("-1.75")), "DSJ0014 pin-1 marker mismatch")


def check_t822_footprint(project):
    root = footprint(project, "TDFN_Maxim_T822-3_2x2mm_P0.5mm_EP0.7x1.38mm")
    pads = children(root, "pad")
    require(Counter(pad[1] for pad in pads) == Counter(map(str, range(1, 10))),
            "T822+3 pad numbers mismatch")
    by_number = {pad[1]: pad for pad in pads}
    for number in range(1, 9):
        if number <= 4:
            position = (D("-0.99"), D("-0.75") + D("0.50") * (number - 1))
        else:
            position = (D("0.99"), D("0.75") - D("0.50") * (number - 5))
        pad = by_number[str(number)]
        require(pad_position(pad) == position, f"T822+3 pad {number} position mismatch")
        require(pad_size(pad) == (D("0.80"), D("0.30")),
                f"T822+3 pad {number} size mismatch")
        require(pad_layers(pad) == ["F.Cu", "F.Paste", "F.Mask"],
                f"T822+3 pad {number} layer mismatch")
    ep = by_number["9"]
    require(pad_position(ep) == (D("0"), D("0")), "T822+3 exposed-pad position mismatch")
    require(pad_size(ep) == (D("0.70"), D("1.38")),
            "T822+3 exposed-pad size mismatch")
    require(pad_layers(ep) == ["F.Cu", "F.Paste", "F.Mask"],
            "T822+3 exposed-pad layers mismatch")
    marker = one(root, "fp_circle", "T822+3 pin-1 marker")
    require(dec(one(marker, "center", "T822+3 pin-1 marker")[1:]) ==
            (D("-1.65"), D("-1.05")), "T822+3 pin-1 marker mismatch")


def check_adg_footprint(project):
    """Project-derived CP-16-22 candidate lands; assembler qualification pending."""
    root = footprint(project, PARTS["ADG4612BCPZ-REEL7"]["footprint"])
    pads = children(root, "pad")
    require(Counter(p[1] for p in pads) == Counter([*map(str, range(17)), "", "", "", ""]),
            "ADG pad numbers/count mismatch; EP must be 0")
    numbered = {p[1]: p for p in pads if p[1]}
    coordinates = ("-0.75", "-0.25", "0.25", "0.75")
    for n in range(1, 17):
        a = D(coordinates[(n-1) % 4])
        if n <= 4: pos, size = (D('-1.45'), a), dec(('0.7', '0.3'))
        elif n <= 8: pos, size = (a, D('1.45')), dec(('0.3', '0.7'))
        elif n <= 12: pos, size = (D('1.45'), -a), dec(('0.7', '0.3'))
        else: pos, size = (-a, D('-1.45')), dec(('0.3', '0.7'))
        pad = numbered[str(n)]
        require(pad_position(pad) == pos and pad_size(pad) == size, f'ADG pad {n} geometry mismatch')
        require(pad_layers(pad) == ['F.Cu', 'F.Paste', 'F.Mask'], f'ADG pad {n} layers mismatch')
    ep = numbered['0']
    require(pad_position(ep) == dec(('0', '0')) and pad_size(ep) == dec(('1.75', '1.75')),
            'ADG exposed-pad geometry mismatch')
    require(pad_layers(ep) == ['F.Cu', 'F.Mask'], 'ADG EP must use separate paste windows')
    windows = [p for p in pads if not p[1]]
    require({pad_position(p) for p in windows} ==
            {(D(x), D(y)) for x in ('-.425', '.425') for y in ('-.425', '.425')},
            'ADG stencil positions mismatch')
    for pad in windows:
        require(pad_size(pad) == dec(('.7', '.7')) and pad_layers(pad) == ['F.Paste'],
                'ADG stencil size/layers mismatch')
    check_replacement_geometry(root, ('1.5','1.5'), ('2.05','2.05'), ('-2.15','-1.25'))



def check_rpw_footprint(project):
    """TI 4225183/A, sheets 2/3: compound corner copper and distinct paste."""
    root = footprint(project, 'VQFN_TI_RPW0010A_2x2mm_HotRod')
    # Explicit independent transcription: n,x,y,w,h,layer group.
    copper = [
        ('1','-.9','-.7','.6','.3'), ('1','-.725','-.875','.25','.65'),
        ('2','-.9','-.225','.6','.25'), ('3','-.9','.225','.6','.25'),
        ('4','-.9','.7','.6','.3'), ('4','-.725','.875','.25','.65'),
        ('5','-.25','0','.3','2.4'), ('6','.25','0','.3','2.4'),
        ('7','.9','.7','.6','.3'), ('7','.725','.875','.25','.65'),
        ('8','.9','.225','.6','.25'), ('9','.9','-.225','.6','.25'),
        ('10','.9','-.7','.6','.3'), ('10','.725','-.875','.25','.65'),
    ]
    stencil = [
        ('-.9','-.6875','.6','.275'), ('-.7125','-.875','.225','.65'),
        ('-.9','.6875','.6','.275'), ('-.7125','.875','.225','.65'),
        ('.9','.6875','.6','.275'), ('.7125','.875','.225','.65'),
        ('.9','-.6875','.6','.275'), ('.7125','-.875','.225','.65'),
        ('-.25','-.63','.28','1.06'), ('-.25','.63','.28','1.06'),
        ('.25','-.63','.28','1.06'), ('.25','.63','.28','1.06'),
    ]
    actual = Counter((p[1], *pad_position(p), *pad_size(p), tuple(pad_layers(p)))
                     for p in children(root,'pad'))
    expected = Counter()
    for n,x,y,w,h in copper:
        layers = ('F.Cu','F.Paste','F.Mask') if n in ('2','3','8','9') else ('F.Cu','F.Mask')
        expected[(n,*dec((x,y,w,h)),layers)] += 1
    for x,y,w,h in stencil:
        expected[('',*dec((x,y,w,h)),('F.Paste',))] += 1
    require(actual == expected, 'RPW copper/stencil geometry or pad identity mismatch')
    check_replacement_geometry(root, ('1','1'), ('1.45','1.45'), ('-1.4','-1.4'))
    # Copper has 10 electrical pads, not an additional exposed ground pad.
    for mpn in ('TPS259472ARPWR','TPS259474ARPWR'):
        require(PARTS[mpn]['pins'][5][0] == 'IN' and PARTS[mpn]['pins'][6][0] == 'OUT',
                'RPW central rails are IN/OUT, not thermal ground')


def check_libraries(project=PROJECT):
    for name in sorted({part["footprint"] for part in PARTS.values()}):
        check_copper_separation(footprint(project, name))
    symbols = check_symbol_libraries(project)
    check_rtw_footprint(project)
    check_rgt_footprint(project)
    check_rse_footprints(project)
    check_drl_footprint(project)
    check_phase_two_footprints(project)
    check_rwb_footprint(project)
    check_dsj_footprint(project)
    check_t822_footprint(project)
    check_adg_footprint(project)
    check_rpw_footprint(project)
    return symbols


def main():
    parser = argparse.ArgumentParser(description=__doc__)
    parser.add_argument("--project-dir", type=Path, default=PROJECT)
    args = parser.parse_args()
    try:
        check_libraries(args.project_dir)
        print("Power library checks passed:")
        print("- TPS259472/474 candidates: distinct pin-2 functions, ten RPW electrical pads, compound corners and segmented stencil")
        print("- ADG4612 candidate: 17 pins including EP 0; project-derived CP-16-22 lands, not approved for assembly")
        print("- permission libraries: 32 gate/supervisor pins plus 6 dual-Schmitt pins; DBV5/DBV6 geometry")
        print("- BQ24074/BQ24392/TS3USB31E: 35 pins, RGT/RSE lands, narrow middle pads, 0.05-mm corner radii")
        print("- distinct power-footprint copper pad bounding boxes are separated")
        print("- 25 BQ25616J pins match the TI RTW pin table and exposed-pad map")
        print("- RTW signal lands and four-way stencil segmentation match TI drawing 4211120-3/D")
        print("- 8 TPS631000 pins and DRL lands match the current TI pin/package drawings")
        print("- DBV, DDF and base-suffix DQA0010A land patterns match current TI drawings")
        print("- 12 TUSB320LAI pins and asymmetric RWB X2QFN copper/stencil maps match TI drawings")
        print("- 15 TPS63020 logical pins and DSJ signal/thermal/stencil maps match TI drawings")
        print("- 9 MAX17048 logical pins and T822+3 land map match Analog Devices drawings")
        print("- USB4505 is checked separately by check-usb-connector.py")
    except (OSError, ValueError, KeyError, IndexError) as error:
        print(f"Power library check failed: {error}", file=sys.stderr)
        return 1
    return 0


if __name__ == "__main__":
    sys.exit(main())
