mulbc/rgb-badge/tools/tests/test_check_kicad.py

# SPDX-License-Identifier: Apache-2.0
"""Regression tests for the shell wrapper, not KiCad or electrical validation."""

import os
from pathlib import Path
import subprocess
import tempfile
import unittest


REPO_ROOT = Path(__file__).resolve().parents[2]
CHECK_SCRIPT = REPO_ROOT / "tools" / "check-kicad.sh"
CLI_STUB = Path(__file__).resolve().parent / "fixtures" / "kicad_cli_stub.py"


class CheckKiCadWrapperTests(unittest.TestCase):
    def setUp(self):
        self.temporary = tempfile.TemporaryDirectory(prefix="rgb-badge-wrapper-test-")
        self.addCleanup(self.temporary.cleanup)
        self.directory = Path(self.temporary.name)
        self.output = self.directory / "review output with spaces"

    def run_check(self, **test_environment):
        environment = {
            key: value for key, value in os.environ.items()
            if not key.startswith("RGB_BADGE_TEST_")
        }
        environment.update({
            "RGB_BADGE_KICAD_CLI": str(CLI_STUB),
            "RGB_BADGE_KICAD_CHECK_OUTPUT": str(self.output),
            **test_environment,
        })
        return subprocess.run(
            ["bash", str(CHECK_SCRIPT)],
            cwd=self.directory,
            env=environment,
            capture_output=True,
            text=True,
            timeout=30,
        )

    def test_separate_raw_views_and_numbered_copies(self):
        result = self.run_check()
        self.assertEqual(result.returncode, 0, result.stdout + result.stderr)
        self.assertEqual(len(list((self.output / "symbols").glob("*.svg"))), 64)
        for view in ("fabrication", "copper", "paste", "numbered", "mechanical"):
            self.assertEqual(len(list((self.output / "footprints" / view).glob("*.svg"))), 3 if view == "numbered" else 35)
        self.assertTrue((self.output / "coupon-erc.rpt").is_file())
        self.assertTrue((self.output / "coupon-matrix.xml").is_file())
        self.assertTrue((self.output / "coupon-schematic.pdf").is_file())

    def test_missing_precision_or_supervisor_export_is_rejected(self):
        for name in ('ERA2AEB3651X_unit1.svg', 'ERA2AEB3481X_unit1.svg',
                     'ERA2AEB1131X_unit1.svg', 'ERJ2RKF6203X_unit1.svg',
                     'R_Panasonic_ERA2_0402.svg', 'ADG4612BCPZ-REEL7_unit1.svg',
                     'LFCSP_ADI_CP16_22_3x3mm_P0.5mm_EP1.75mm.svg',
                     'DFE252012P-1R0M=P2_unit1.svg', 'L_Murata_DFE252012P.svg'):
            with self.subTest(name=name):
                self.output = self.directory / name
                result = self.run_check(RGB_BADGE_TEST_MISSING_NAMED=name)
                self.assertEqual(result.returncode, 1)
                self.assertIn('Expected non-empty', result.stderr)
                self.assertFalse((self.output / 'coupon-erc.rpt').exists())

    def test_numbering_failure_is_not_hidden(self):
        result = self.run_check(RGB_BADGE_TEST_BAD_LABELS="1")
        self.assertEqual(result.returncode, 1)
        self.assertIn("Numbered footprint review failed", result.stderr)
        self.assertFalse((self.output / "coupon-erc.rpt").exists())

    def test_missing_specific_copper_file_is_rejected(self):
        result = self.run_check(RGB_BADGE_TEST_MISSING="1")
        self.assertEqual(result.returncode, 1)
        self.assertIn("Expected non-empty SVG", result.stderr)
        self.assertIn("copper/LED_QTBrightek_QBLP1515A-RGB2A.svg", result.stderr)
        self.assertFalse((self.output / "coupon-erc.rpt").exists())

    def test_empty_specific_copper_file_is_rejected(self):
        result = self.run_check(RGB_BADGE_TEST_EMPTY="1")
        self.assertEqual(result.returncode, 1)
        self.assertIn("Expected non-empty SVG", result.stderr)

    def test_export_failure_is_not_hidden(self):
        for stage in ("copper", "mechanical"):
            with self.subTest(stage=stage):
                self.output = self.directory / stage
                result = self.run_check(RGB_BADGE_TEST_FAIL=stage)
                self.assertEqual(result.returncode, 7)
                self.assertNotIn("ERC passed", result.stdout)

    def test_missing_usb_connector_mechanical_export_is_rejected(self):
        result = self.run_check(RGB_BADGE_TEST_MISSING_USB_CONNECTOR="1")
        self.assertEqual(result.returncode, 1)
        self.assertIn("Expected non-empty USB connector footprint SVG", result.stderr)
        self.assertIn("footprints/mechanical", result.stderr)
        self.assertFalse((self.output / "coupon-erc.rpt").exists())

    def test_erc_failure_is_not_hidden(self):
        result = self.run_check(RGB_BADGE_TEST_FAIL="sch/erc")
        self.assertEqual(result.returncode, 5)
        self.assertNotIn("ERC passed", result.stdout)

    def test_retired_usb_boundary_warnings_are_rejected(self):
        result = self.run_check(RGB_BADGE_TEST_USB_BOUNDARY_ERC="1")
        self.assertEqual(result.returncode, 1)
        self.assertIn("Unexpected ERC violation set", result.stderr)

    def test_unexpected_erc_warning_is_not_hidden(self):
        result = self.run_check(RGB_BADGE_TEST_UNEXPECTED_ERC="1")
        self.assertEqual(result.returncode, 1)
        self.assertIn("Unexpected ERC violation set", result.stderr)
        self.assertFalse((self.output / "coupon-matrix.xml").exists())

    def test_bad_matrix_netlist_is_not_hidden(self):
        result = self.run_check(RGB_BADGE_TEST_BAD_MATRIX="1")
        self.assertEqual(result.returncode, 1)
        self.assertIn('Controller check failed', result.stderr)
        self.assertFalse((self.output / 'coupon-schematic.pdf').exists())

    def test_netlist_and_pdf_export_failures_are_not_hidden(self):
        for stage in ('netlist', 'pdf'):
            with self.subTest(stage=stage):
                self.output = self.directory / stage
                result = self.run_check(RGB_BADGE_TEST_FAIL=stage)
                self.assertEqual(result.returncode, 7)
                self.assertNotIn('matrix connectivity and Coupon Rev A ERC passed', result.stdout)

    def test_bad_driver_netlist_is_not_hidden(self):
        result = self.run_check(RGB_BADGE_TEST_BAD_DRIVER="1")
        self.assertEqual(result.returncode, 1)
        self.assertIn("Controller check failed", result.stderr)
        self.assertFalse((self.output / "coupon-schematic.pdf").exists())

    def test_bad_row_netlist_is_not_hidden(self):
        result = self.run_check(RGB_BADGE_TEST_BAD_ROWS="1")
        self.assertEqual(result.returncode, 1)
        self.assertIn("Controller check failed", result.stderr)
        self.assertFalse((self.output / "coupon-schematic.pdf").exists())

    def test_bad_controller_netlist_is_not_hidden(self):
        result = self.run_check(RGB_BADGE_TEST_BAD_CONTROLLER="1")
        self.assertEqual(result.returncode, 1)
        self.assertIn("Controller check failed", result.stderr)
        self.assertFalse((self.output / "coupon-schematic.pdf").exists())

    def test_missing_driver_paste_export_is_rejected(self):
        result = self.run_check(RGB_BADGE_TEST_MISSING_PASTE="1")
        self.assertEqual(result.returncode, 1)
        self.assertIn("driver footprint SVG", result.stderr)
        self.assertFalse((self.output / "coupon-erc.rpt").exists())

    def test_wrong_kicad_version_is_rejected(self):
        result = self.run_check(RGB_BADGE_TEST_VERSION="9.0.0")
        self.assertEqual(result.returncode, 2)
        self.assertIn("Expected stable KiCad 10.0.x", result.stderr)
        self.assertFalse(self.output.exists())

    def test_existing_output_is_preserved(self):
        self.output.mkdir()
        sentinel = self.output / "keep.txt"
        sentinel.write_text("Existing review evidence\n", encoding="utf-8")
        result = self.run_check()
        self.assertEqual(result.returncode, 2)
        self.assertIn("path that does not exist", result.stderr)
        self.assertEqual(sentinel.read_text(encoding="utf-8"), "Existing review evidence\n")


if __name__ == "__main__":
    unittest.main()
